kuanwoo/SYMPL64_FloatingPoint_RISC-/FloPoCo_operators/Exp_Clk9.vhdl

-- vagrant@vagrant-ubuntu-trusty-32:~/flopoco-3.0.beta5$ ./flopoco -name=Exp_Clk -frequency=200 -useHardMult=no FPExp 9 23
-- Warning: the given expression is not a constant but an expression to evaluate. A faithful evaluation to 10000 bits will be used.
-- Warning: the given expression is not a constant but an expression to evaluate. A faithful evaluation to 10000 bits will be used.
-- Updating entity name to: Exp_Clk
-- 
-- Final report:
-- Entity SmallMultTableP3x3r6XuYu
--    Not pipelined
-- Entity Compressor_6_3_c
--    Not pipelined
-- Entity Compressor_14_3_d
--    Not pipelined
-- Entity Compressor_4_3_e
--    Not pipelined
-- Entity Compressor_23_3_f
--    Not pipelined
-- Entity Compressor_3_2_a
--    Not pipelined
-- |---Entity LeftShifter_24_by_max_34_uid3
-- |      Not pipelined
-- |   |---Entity FixRealKCM_M3_7_0_1_log_2_unsigned_Table_1
-- |   |      Not pipelined
-- |   |---Entity FixRealKCM_M3_7_0_1_log_2_unsigned_Table_0
-- |   |      Not pipelined
-- |   |---Entity IntAdder_13_f200_uid11
-- |   |      Not pipelined
-- |---Entity FixRealKCM_M3_7_0_1_log_2_unsigned
-- |      Pipeline depth = 1
-- |   |---Entity FixRealKCM_0_8_M26_log_2_unsigned_Table_1
-- |   |      Not pipelined
-- |   |---Entity FixRealKCM_0_8_M26_log_2_unsigned_Table_0
-- |   |      Not pipelined
-- |   |---Entity IntAdder_35_f200_uid24
-- |   |      Pipeline depth = 1
-- |---Entity FixRealKCM_0_8_M26_log_2_unsigned
-- |      Pipeline depth = 1
-- |---Entity IntAdder_26_f219_uid32
-- |      Not pipelined
-- |---Entity MagicSPExpTable
-- |      Not pipelined
-- |---Entity IntAdder_18_f200_uid41
-- |      Not pipelined
-- |---Entity IntAdder_18_f200_uid48
-- |      Not pipelined
-- |   |---Entity IntAdder_24_f200_uid155
-- |   |      Not pipelined
-- |---Entity IntMultiplier_UsingDSP_17_18_19_unsigned_uid55
-- |      Pipeline depth = 1
-- |---Entity IntAdder_27_f200_uid163
-- |      Not pipelined
-- |---Entity IntAdder_34_f200_uid170
-- |      Not pipelined
-- Entity Exp_Clk
--    Pipeline depth = 6
-- Output file: flopoco.vhdl
--------------------------------------------------------------------------------
--                          SmallMultTableP3x3r6XuYu
-- This operator is part of the Infinite Virtual Library FloPoCoLib
-- All rights reserved
-- Authors: Florent de Dinechin (2007-2012)
--------------------------------------------------------------------------------
library ieee;
use ieee.std_logic_1164.all;
use ieee.numeric_std.all;
library work;
entity SmallMultTableP3x3r6XuYu is
   port ( clk, rst : in std_logic;
          X : in  std_logic_vector(5 downto 0);
          Y : out  std_logic_vector(5 downto 0)   );
end entity;

architecture arch of SmallMultTableP3x3r6XuYu is
begin
  with X select  Y <=
   "000000" when "000000",
   "000000" when "000001",
   "000000" when "000010",
   "000000" when "000011",
   "000000" when "000100",
   "000000" when "000101",
   "000000" when "000110",
   "000000" when "000111",
   "000000" when "001000",
   "000001" when "001001",
   "000010" when "001010",
   "000011" when "001011",
   "000100" when "001100",
   "000101" when "001101",
   "000110" when "001110",
   "000111" when "001111",
   "000000" when "010000",
   "000010" when "010001",
   "000100" when "010010",
   "000110" when "010011",
   "001000" when "010100",
   "001010" when "010101",
   "001100" when "010110",
   "001110" when "010111",
   "000000" when "011000",
   "000011" when "011001",
   "000110" when "011010",
   "001001" when "011011",
   "001100" when "011100",
   "001111" when "011101",
   "010010" when "011110",
   "010101" when "011111",
   "000000" when "100000",
   "000100" when "100001",
   "001000" when "100010",
   "001100" when "100011",
   "010000" when "100100",
   "010100" when "100101",
   "011000" when "100110",
   "011100" when "100111",
   "000000" when "101000",
   "000101" when "101001",
   "001010" when "101010",
   "001111" when "101011",
   "010100" when "101100",
   "011001" when "101101",
   "011110" when "101110",
   "100011" when "101111",
   "000000" when "110000",
   "000110" when "110001",
   "001100" when "110010",
   "010010" when "110011",
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
use ieee.std_logic_unsigned.all;
library std;
use std.textio.all;
library work;

entity Compressor_14_3_d is
   port ( X0 : in  std_logic_vector(3 downto 0);
          X1 : in  std_logic_vector(0 downto 0);
          R : out  std_logic_vector(2 downto 0)   );
end entity;

architecture arch of Compressor_14_3_d is
signal X :  std_logic_vector(4 downto 0);
begin
   X <=X1 & X0 ;
   with X select R <=
      "000" when "00000",
      "001" when "00001",
      "001" when "00010",
      "010" when "00011",
      "001" when "00100",
      "010" when "00101",
      "010" when "00110",
      "011" when "00111",
      "001" when "01000",
      "010" when "01001",
      "010" when "01010",
      "011" when "01011",
      "010" when "01100",
      "011" when "01101",
      "011" when "01110",
      "100" when "01111",
      "010" when "10000",
      "011" when "10001",
      "011" when "10010",
      "100" when "10011",
      "011" when "10100",
      "100" when "10101",
      "100" when "10110",
      "101" when "10111",
      "011" when "11000",
      "100" when "11001",
      "100" when "11010",
      "101" when "11011",
      "100" when "11100",
      "101" when "11101",
      "101" when "11110",
      "110" when "11111",
      "---" when others;

end architecture;

--------------------------------------------------------------------------------
--                               Compressor_4_3_e
-- This operator is part of the Infinite Virtual Library FloPoCoLib
-- All rights reserved
-- Authors: Bogdan Popa, Illyes Kinga, 2012
--------------------------------------------------------------------------------
-- combinatorial

library ieee;
use ieee.std_logic_1164.all;
use ieee.std_logic_arith.all;
use ieee.std_logic_unsigned.all;
library std;
use std.textio.all;
library work;

entity Compressor_4_3_e is
   port ( X0 : in  std_logic_vector(3 downto 0);
          R : out  std_logic_vector(2 downto 0)   );
end entity;

architecture arch of Compressor_4_3_e is
signal X :  std_logic_vector(3 downto 0);
begin
   X <=X0 ;
   with X select R <=
      "000" when "0000",
      "001" when "0001",
      "001" when "0010",
      "010" when "0011",
      "001" when "0100",
      "010" when "0101",
      "010" when "0110",
      "011" when "0111",
      "001" when "1000",
      "010" when "1001",
      "010" when "1010",
      "011" when "1011",
      "010" when "1100",
      "011" when "1101",
      "011" when "1110",
      "100" when "1111",
      "---" when others;

end architecture;

--------------------------------------------------------------------------------
--                              Compressor_23_3_f
-- This operator is part of the Infinite Virtual Library FloPoCoLib
-- All rights reserved
-- Authors: Bogdan Popa, Illyes Kinga, 2012
--------------------------------------------------------------------------------
-- combinatorial

library ieee;
use ieee.std_logic_1164.all;
use ieee.std_logic_arith.all;
use ieee.std_logic_unsigned.all;
library std;
use std.textio.all;
library work;

entity Compressor_23_3_f is
   port ( X0 : in  std_logic_vector(2 downto 0);
          X1 : in  std_logic_vector(1 downto 0);
          R : out  std_logic_vector(2 downto 0)   );
end entity;

architecture arch of Compressor_23_3_f is
signal X :  std_logic_vector(4 downto 0);
begin
   X <=X1 & X0 ;
   with X select R <=
      "000" when "00000",
      "001" when "00001",
      "001" when "00010",
      "010" when "00011",
      "001" when "00100",
      "010" when "00101",
      "010" when "00110",
      "011" when "00111",
      "010" when "01000",
      "011" when "01001",
      "011" when "01010",
      "100" when "01011",
      "011" when "01100",
      "100" when "01101",
      "100" when "01110",
      "101" when "01111",
      "010" when "10000",
      "011" when "10001",
      "011" when "10010",
      "100" when "10011",
      "011" when "10100",
      "100" when "10101",
      "100" when "10110",
      "101" when "10111",
      "100" when "11000",
      "101" when "11001",
      "101" when "11010",
      "110" when "11011",
      "101" when "11100",
      "110" when "11101",
      "110" when "11110",
      "111" when "11111",
      "---" when others;

end architecture;

--------------------------------------------------------------------------------
--                               Compressor_3_2_a
-- This operator is part of the Infinite Virtual Library FloPoCoLib
-- All rights reserved
-- Authors: Bogdan Popa, Illyes Kinga, 2012
--------------------------------------------------------------------------------
-- combinatorial

library ieee;
use ieee.std_logic_1164.all;
use ieee.std_logic_arith.all;
use ieee.std_logic_unsigned.all;
library std;
use std.textio.all;
library work;

entity Compressor_3_2_a is
   port ( X0 : in  std_logic_vector(2 downto 0);
          R : out  std_logic_vector(1 downto 0)   );
end entity;

architecture arch of Compressor_3_2_a is
signal X :  std_logic_vector(2 downto 0);
begin
   X <=X0 ;
   with X select R <=
      "00" when "000",
      "01" when "001",
      "01" when "010",
      "10" when "011",
      "01" when "100",
      "10" when "101",
      "10" when "110",
      "11" when "111",
      "--" when others;

end architecture;

--------------------------------------------------------------------------------
--                       LeftShifter_24_by_max_34_uid3
-- This operator is part of the Infinite Virtual Library FloPoCoLib
-- All rights reserved
-- Authors: Bogdan Pasca, Florent de Dinechin (2008-2011)
--------------------------------------------------------------------------------
-- Pipeline depth: 0 cycles

library ieee;
use ieee.std_logic_1164.all;
use ieee.std_logic_arith.all;
use ieee.std_logic_unsigned.all;
library std;
use std.textio.all;
library work;

entity LeftShifter_24_by_max_34_uid3 is
   port ( clk, rst : in std_logic;
          X : in  std_logic_vector(23 downto 0);
          S : in  std_logic_vector(5 downto 0);
          R : out  std_logic_vector(57 downto 0)   );
end entity;

architecture arch of LeftShifter_24_by_max_34_uid3 is
signal level0 :  std_logic_vector(23 downto 0);
signal ps :  std_logic_vector(5 downto 0);
signal level1 :  std_logic_vector(24 downto 0);
signal level2 :  std_logic_vector(26 downto 0);
signal level3 :  std_logic_vector(30 downto 0);
signal level4 :  std_logic_vector(38 downto 0);
signal level5 :  std_logic_vector(54 downto 0);
signal level6 :  std_logic_vector(86 downto 0);
begin
   process(clk)
      begin
         if clk'event and clk = '1' then
         end if;
      end process;
   level0<= X;
   ps<= S;
   level1<= level0 & (0 downto 0 => '0') when ps(0)= '1' else     (0 downto 0 => '0') & level0;
   level2<= level1 & (1 downto 0 => '0') when ps(1)= '1' else     (1 downto 0 => '0') & level1;
   level3<= level2 & (3 downto 0 => '0') when ps(2)= '1' else     (3 downto 0 => '0') & level2;
   level4<= level3 & (7 downto 0 => '0') when ps(3)= '1' else     (7 downto 0 => '0') & level3;
   level5<= level4 & (15 downto 0 => '0') when ps(4)= '1' else     (15 downto 0 => '0') & level4;
   level6<= level5 & (31 downto 0 => '0') when ps(5)= '1' else     (31 downto 0 => '0') & level5;
   R <= level6(57 downto 0);
end architecture;

--------------------------------------------------------------------------------
--                 FixRealKCM_M3_7_0_1_log_2_unsigned_Table_1
-- This operator is part of the Infinite Virtual Library FloPoCoLib
-- All rights reserved
-- Authors: Florent de Dinechin (2007-2012)
--------------------------------------------------------------------------------
library ieee;
use ieee.std_logic_1164.all;
use ieee.numeric_std.all;
library work;
entity FixRealKCM_M3_7_0_1_log_2_unsigned_Table_1 is
   port ( clk, rst : in std_logic;
          X : in  std_logic_vector(4 downto 0);
          Y : out  std_logic_vector(12 downto 0)   );
end entity;

architecture arch of FixRealKCM_M3_7_0_1_log_2_unsigned_Table_1 is
begin
  with X select  Y <=
   "0000000001000" when "00000",
   "0000011000001" when "00001",
   "0000101111001" when "00010",
   "0001000110010" when "00011",
   "0001011101011" when "00100",
   "0001110100011" when "00101",
   "0010001011100" when "00110",
   "0010100010101" when "00111",
   "0010111001101" when "01000",
   "0011010000110" when "01001",
   "0011100111111" when "01010",
   "0011111110111" when "01011",
   "0100010110000" when "01100",
   "0100101101001" when "01101",
   "0101000100001" when "01110",
   "0101011011010" when "01111",
   "0101110010011" when "10000",
   "0110001001011" when "10001",
   "0110100000100" when "10010",
   "0110110111101" when "10011",
   "0111001110101" when "10100",
   "0111100101110" when "10101",
   "0111111100111" when "10110",
   "1000010011111" when "10111",
   "1000101011000" when "11000",
   "1001000010001" when "11001",
   "1001011001001" when "11010",
   "1001110000010" when "11011",
   "1010000111011" when "11100",
   "1010011110011" when "11101",
   "1010110101100" when "11110",
   "1011001100101" when "11111",
   "-------------" when others;
end architecture;

--------------------------------------------------------------------------------
--                 FixRealKCM_M3_7_0_1_log_2_unsigned_Table_0
-- This operator is part of the Infinite Virtual Library FloPoCoLib
-- All rights reserved
-- Authors: Florent de Dinechin (2007-2012)
--------------------------------------------------------------------------------
library ieee;
use ieee.std_logic_1164.all;
use ieee.numeric_std.all;
library work;
entity FixRealKCM_M3_7_0_1_log_2_unsigned_Table_0 is
   port ( clk, rst : in std_logic;
          X : in  std_logic_vector(5 downto 0);
          Y : out  std_logic_vector(7 downto 0)   );
end entity;

architecture arch of FixRealKCM_M3_7_0_1_log_2_unsigned_Table_0 is
begin
  with X select  Y <=
   "00000000" when "000000",
   "00000011" when "000001",
   "00000110" when "000010",
   "00001001" when "000011",
   "00001100" when "000100",
   "00001110" when "000101",
   "00010001" when "000110",
   "00010100" when "000111",
   "00010111" when "001000",
   "00011010" when "001001",
   "00011101" when "001010",
   "00100000" when "001011",
   "00100011" when "001100",
   "00100110" when "001101",
   "00101000" when "001110",
   "00101011" when "001111",
   "00101110" when "010000",
   "00110001" when "010001",
   "00110100" when "010010",
   "00110111" when "010011",
   "00111010" when "010100",
   "00111101" when "010101",
   "00111111" when "010110",
   "01000010" when "010111",
   "01000101" when "011000",
   "01001000" when "011001",
   "01001011" when "011010",
   "01001110" when "011011",
   "01010001" when "011100",
   "01010100" when "011101",
   "01010111" when "011110",
   "01011001" when "011111",
   "01011100" when "100000",
   "01011111" when "100001",
   "01100010" when "100010",
   "01100101" when "100011",
   "01101000" when "100100",
   "01101011" when "100101",
   "01101110" when "100110",
   "01110001" when "100111",
   "01110011" when "101000",
   "01110110" when "101001",
   "01111001" when "101010",
   "01111100" when "101011",
   "01111111" when "101100",
   "10000010" when "101101",
   "10000101" when "101110",
   "10001000" when "101111",
   "10001010" when "110000",
   "10001101" when "110001",
   "10010000" when "110010",
   "10010011" when "110011",
   "10010110" when "110100",
   "10011001" when "110101",
   "10011100" when "110110",
   "10011111" when "110111",
   "10100010" when "111000",
   "10100100" when "111001",
   "10100111" when "111010",
   "10101010" when "111011",
   "10101101" when "111100",
   "10110000" when "111101",
   "10110011" when "111110",
   "10110110" when "111111",
   "--------" when others;
end architecture;

--------------------------------------------------------------------------------
--                           IntAdder_13_f200_uid11
--                    (IntAdderAlternative_13_f200_uid15)
-- This operator is part of the Infinite Virtual Library FloPoCoLib
-- All rights reserved
-- Authors: Bogdan Pasca, Florent de Dinechin (2008-2010)
--------------------------------------------------------------------------------
-- Pipeline depth: 0 cycles

library ieee;
use ieee.std_logic_1164.all;
use ieee.std_logic_arith.all;
use ieee.std_logic_unsigned.all;
library std;
use std.textio.all;
library work;

entity IntAdder_13_f200_uid11 is
   port ( clk, rst : in std_logic;
          X : in  std_logic_vector(12 downto 0);
          Y : in  std_logic_vector(12 downto 0);
          Cin : in  std_logic;
          R : out  std_logic_vector(12 downto 0)   );
end entity;

architecture arch of IntAdder_13_f200_uid11 is
begin
   process(clk)
      begin
         if clk'event and clk = '1' then
         end if;
      end process;
   --Alternative
    R <= X + Y + Cin;
end architecture;

--------------------------------------------------------------------------------
--                     FixRealKCM_M3_7_0_1_log_2_unsigned
-- This operator is part of the Infinite Virtual Library FloPoCoLib
-- All rights reserved
-- Authors:
--------------------------------------------------------------------------------
-- Pipeline depth: 1 cycles

library ieee;
use ieee.std_logic_1164.all;
use ieee.std_logic_arith.all;
use ieee.std_logic_unsigned.all;
library std;
use std.textio.all;
library work;

entity FixRealKCM_M3_7_0_1_log_2_unsigned is
   port ( clk, rst : in std_logic;
          X : in  std_logic_vector(10 downto 0);
          R : out  std_logic_vector(8 downto 0)   );
end entity;

architecture arch of FixRealKCM_M3_7_0_1_log_2_unsigned is
   component FixRealKCM_M3_7_0_1_log_2_unsigned_Table_0 is
      port ( clk, rst : in std_logic;
             X : in  std_logic_vector(5 downto 0);
             Y : out  std_logic_vector(7 downto 0)   );
   end component;

   component FixRealKCM_M3_7_0_1_log_2_unsigned_Table_1 is
      port ( clk, rst : in std_logic;
             X : in  std_logic_vector(4 downto 0);
             Y : out  std_logic_vector(12 downto 0)   );
   end component;

   component IntAdder_13_f200_uid11 is
      port ( clk, rst : in std_logic;
             X : in  std_logic_vector(12 downto 0);
             Y : in  std_logic_vector(12 downto 0);
             Cin : in  std_logic;
             R : out  std_logic_vector(12 downto 0)   );
   end component;

signal d1 :  std_logic_vector(4 downto 0);
signal d0 :  std_logic_vector(5 downto 0);
signal pp0, pp0_d1 :  std_logic_vector(7 downto 0);
signal pp1, pp1_d1 :  std_logic_vector(12 downto 0);
signal addOp0 :  std_logic_vector(12 downto 0);
signal OutRes :  std_logic_vector(12 downto 0);
attribute rom_extract: string;
attribute rom_style: string;
attribute rom_extract of FixRealKCM_M3_7_0_1_log_2_unsigned_Table_0: component is "yes";
attribute rom_extract of FixRealKCM_M3_7_0_1_log_2_unsigned_Table_1: component is "yes";
attribute rom_style of FixRealKCM_M3_7_0_1_log_2_unsigned_Table_0: component is "distributed";
attribute rom_style of FixRealKCM_M3_7_0_1_log_2_unsigned_Table_1: component is "distributed";
begin
   process(clk)
      begin
         if clk'event and clk = '1' then
            pp0_d1 <=  pp0;
            pp1_d1 <=  pp1;
         end if;
      end process;
   d1 <= X(10 downto 6);
   d0 <= X(5 downto 0);
   KCMTable_0: FixRealKCM_M3_7_0_1_log_2_unsigned_Table_0  -- pipelineDepth=0 maxInDelay=0
      port map ( clk  => clk,
                 rst  => rst,
                 X => d0,
                 Y => pp0);
   KCMTable_1: FixRealKCM_M3_7_0_1_log_2_unsigned_Table_1  -- pipelineDepth=0 maxInDelay=0
      port map ( clk  => clk,
                 rst  => rst,
                 X => d1,
                 Y => pp1);
   ----------------Synchro barrier, entering cycle 1----------------
   addOp0 <= (12 downto 8 => '0') & pp0_d1;
   Result_Adder: IntAdder_13_f200_uid11  -- pipelineDepth=0 maxInDelay=1.08008e-09
      port map ( clk  => clk,
                 rst  => rst,
                 Cin => '0',
                 R => OutRes,
                 X => addOp0,
                 Y => pp1_d1);
   R <= OutRes(12 downto 4);
end architecture;

--------------------------------------------------------------------------------
--                 FixRealKCM_0_8_M26_log_2_unsigned_Table_1
-- This operator is part of the Infinite Virtual Library FloPoCoLib
-- All rights reserved
-- Authors: Florent de Dinechin (2007-2012)
--------------------------------------------------------------------------------
library ieee;
use ieee.std_logic_1164.all;
use ieee.numeric_std.all;
library work;
entity FixRealKCM_0_8_M26_log_2_unsigned_Table_1 is
   port ( clk, rst : in std_logic;
          X : in  std_logic_vector(2 downto 0);
          Y : out  std_logic_vector(34 downto 0)   );
end entity;

architecture arch of FixRealKCM_0_8_M26_log_2_unsigned_Table_1 is
begin
  with X select  Y <=
   "00000000000000000000000000000000000" when "000",
   "00010110001011100100001011111111000" when "001",
   "00101100010111001000010111111110000" when "010",
   "01000010100010101100100011111100111" when "011",
   "01011000101110010000101111111011111" when "100",
   "01101110111001110100111011111010111" when "101",
   "10000101000101011001000111111001111" when "110",
   "10011011010000111101010011111000111" when "111",
   "-----------------------------------" when others;
end architecture;

--------------------------------------------------------------------------------
--                 FixRealKCM_0_8_M26_log_2_unsigned_Table_0
-- This operator is part of the Infinite Virtual Library FloPoCoLib
-- All rights reserved
-- Authors: Florent de Dinechin (2007-2012)
--------------------------------------------------------------------------------
library ieee;
use ieee.std_logic_1164.all;
use ieee.numeric_std.all;
library work;
entity FixRealKCM_0_8_M26_log_2_unsigned_Table_0 is
   port ( clk, rst : in std_logic;
          X : in  std_logic_vector(5 downto 0);
          Y : out  std_logic_vector(31 downto 0)   );
end entity;

architecture arch of FixRealKCM_0_8_M26_log_2_unsigned_Table_0 is
begin
  with X select  Y <=
   "00000000000000000000000000000000" when "000000",
   "00000010110001011100100001100000" when "000001",
   "00000101100010111001000011000000" when "000010",
   "00001000010100010101100100100000" when "000011",
   "00001011000101110010000101111111" when "000100",
   "00001101110111001110100111011111" when "000101",
   "00010000101000101011001000111111" when "000110",
   "00010011011010000111101010011111" when "000111",
   "00010110001011100100001011111111" when "001000",
   "00011000111101000000101101011111" when "001001",
   "00011011101110011101001110111111" when "001010",
   "00011110011111111001110000011111" when "001011",
   "00100001010001010110010001111110" when "001100",
   "00100100000010110010110011011110" when "001101",
   "00100110110100001111010100111110" when "001110",
   "00101001100101101011110110011110" when "001111",
   "00101100010111001000010111111110" when "010000",
   "00101111001000100100111001011110" when "010001",
   "00110001111010000001011010111110" when "010010",
   "00110100101011011101111100011110" when "010011",
   "00110111011100111010011101111101" when "010100",
   "00111010001110010110111111011101" when "010101",
   "00111100111111110011100000111101" when "010110",
   "00111111110001010000000010011101" when "010111",
   "01000010100010101100100011111101" when "011000",
   "01000101010100001001000101011101" when "011001",
   "01001000000101100101100110111101" when "011010",
   "01001010110111000010001000011101" when "011011",
   "01001101101000011110101001111100" when "011100",
   "01010000011001111011001011011100" when "011101",
   "01010011001011010111101100111100" when "011110",
   "01010101111100110100001110011100" when "011111",
   "01011000101110010000101111111100" when "100000",
   "01011011011111101101010001011100" when "100001",
   "01011110010001001001110010111100" when "100010",
   "01100001000010100110010100011100" when "100011",
   "01100011110100000010110101111011" when "100100",
   "01100110100101011111010111011011" when "100101",
   "01101001010110111011111000111011" when "100110",
   "01101100001000011000011010011011" when "100111",
   "01101110111001110100111011111011" when "101000",
   "01110001101011010001011101011011" when "101001",
   "01110100011100101101111110111011" when "101010",
   "01110111001110001010100000011011" when "101011",
   "01111001111111100111000001111010" when "101100",
   "01111100110001000011100011011010" when "101101",
   "01111111100010100000000100111010" when "101110",
   "10000010010011111100100110011010" when "101111",
   "10000101000101011001000111111010" when "110000",
   "10000111110110110101101001011010" when "110001",
   "10001010101000010010001010111010" when "110010",
   "10001101011001101110101100011001" when "110011",
   "10010000001011001011001101111001" when "110100",
   "10010010111100100111101111011001" when "110101",
   "10010101101110000100010000111001" when "110110",
   "10011000011111100000110010011001" when "110111",
   "10011011010000111101010011111001" when "111000",
   "10011110000010011001110101011001" when "111001",
   "10100000110011110110010110111001" when "111010",
   "10100011100101010010111000011000" when "111011",
   "10100110010110101111011001111000" when "111100",
   "10101001001000001011111011011000" when "111101",
   "10101011111001101000011100111000" when "111110",
   "10101110101011000100111110011000" when "111111",
   "--------------------------------" when others;
end architecture;

--------------------------------------------------------------------------------
--                           IntAdder_35_f200_uid24
--                     (IntAdderClassical_35_f200_uid26)
-- This operator is part of the Infinite Virtual Library FloPoCoLib
-- All rights reserved
-- Authors: Bogdan Pasca, Florent de Dinechin (2008-2010)
--------------------------------------------------------------------------------
-- Pipeline depth: 1 cycles

library ieee;
use ieee.std_logic_1164.all;
use ieee.std_logic_arith.all;
use ieee.std_logic_unsigned.all;
library std;
use std.textio.all;
library work;

entity IntAdder_35_f200_uid24 is
   port ( clk, rst : in std_logic;
          X : in  std_logic_vector(34 downto 0);
          Y : in  std_logic_vector(34 downto 0);
          Cin : in  std_logic;
          R : out  std_logic_vector(34 downto 0)   );
end entity;

architecture arch of IntAdder_35_f200_uid24 is
signal X_d1 :  std_logic_vector(34 downto 0);
signal Y_d1 :  std_logic_vector(34 downto 0);
signal Cin_d1 :  std_logic;
begin
   process(clk)
      begin
         if clk'event and clk = '1' then
            X_d1 <=  X;
            Y_d1 <=  Y;
            Cin_d1 <=  Cin;
         end if;
      end process;
   --Classical
   ----------------Synchro barrier, entering cycle 1----------------
    R <= X_d1 + Y_d1 + Cin_d1;
end architecture;

--------------------------------------------------------------------------------
--                     FixRealKCM_0_8_M26_log_2_unsigned
-- This operator is part of the Infinite Virtual Library FloPoCoLib
-- All rights reserved
-- Authors:
--------------------------------------------------------------------------------
-- Pipeline depth: 1 cycles

library ieee;
use ieee.std_logic_1164.all;
use ieee.std_logic_arith.all;
use ieee.std_logic_unsigned.all;
library std;
use std.textio.all;
library work;

entity FixRealKCM_0_8_M26_log_2_unsigned is
   port ( clk, rst : in std_logic;
          X : in  std_logic_vector(8 downto 0);
          R : out  std_logic_vector(34 downto 0)   );
end entity;

architecture arch of FixRealKCM_0_8_M26_log_2_unsigned is
   component FixRealKCM_0_8_M26_log_2_unsigned_Table_0 is
      port ( clk, rst : in std_logic;
             X : in  std_logic_vector(5 downto 0);
             Y : out  std_logic_vector(31 downto 0)   );
   end component;

   component FixRealKCM_0_8_M26_log_2_unsigned_Table_1 is
      port ( clk, rst : in std_logic;
             X : in  std_logic_vector(2 downto 0);
             Y : out  std_logic_vector(34 downto 0)   );
   end component;

   component IntAdder_35_f200_uid24 is
      port ( clk, rst : in std_logic;
             X : in  std_logic_vector(34 downto 0);
             Y : in  std_logic_vector(34 downto 0);
             Cin : in  std_logic;
             R : out  std_logic_vector(34 downto 0)   );
   end component;

signal d1 :  std_logic_vector(2 downto 0);
signal d0 :  std_logic_vector(5 downto 0);
signal pp0 :  std_logic_vector(31 downto 0);
signal pp1 :  std_logic_vector(34 downto 0);
signal addOp0 :  std_logic_vector(34 downto 0);
signal OutRes :  std_logic_vector(34 downto 0);
attribute rom_extract: string;
attribute rom_style: string;
attribute rom_extract of FixRealKCM_0_8_M26_log_2_unsigned_Table_0: component is "yes";
attribute rom_extract of FixRealKCM_0_8_M26_log_2_unsigned_Table_1: component is "yes";
attribute rom_style of FixRealKCM_0_8_M26_log_2_unsigned_Table_0: component is "distributed";
attribute rom_style of FixRealKCM_0_8_M26_log_2_unsigned_Table_1: component is "distributed";
begin
   process(clk)
      begin
         if clk'event and clk = '1' then
         end if;
      end process;
   d1 <= X(8 downto 6);
   d0 <= X(5 downto 0);
   KCMTable_0: FixRealKCM_0_8_M26_log_2_unsigned_Table_0  -- pipelineDepth=0 maxInDelay=0
      port map ( clk  => clk,
                 rst  => rst,
                 X => d0,
                 Y => pp0);
   KCMTable_1: FixRealKCM_0_8_M26_log_2_unsigned_Table_1  -- pipelineDepth=0 maxInDelay=0
      port map ( clk  => clk,
                 rst  => rst,
                 X => d1,
                 Y => pp1);
   addOp0 <= (34 downto 32 => '0') & pp0;
   Result_Adder: IntAdder_35_f200_uid24  -- pipelineDepth=1 maxInDelay=3.93836e-09
      port map ( clk  => clk,
                 rst  => rst,
                 Cin => '0',
                 R => OutRes,
                 X => addOp0,
                 Y => pp1);
   ----------------Synchro barrier, entering cycle 1----------------
   R <= OutRes(34 downto 0);
end architecture;

--------------------------------------------------------------------------------
--                           IntAdder_26_f219_uid32
--                    (IntAdderAlternative_26_f219_uid36)
-- This operator is part of the Infinite Virtual Library FloPoCoLib
-- All rights reserved
-- Authors: Bogdan Pasca, Florent de Dinechin (2008-2010)
--------------------------------------------------------------------------------
-- Pipeline depth: 0 cycles

library ieee;
use ieee.std_logic_1164.all;
use ieee.std_logic_arith.all;
use ieee.std_logic_unsigned.all;
library std;
use std.textio.all;
library work;

entity IntAdder_26_f219_uid32 is
   port ( clk, rst : in std_logic;
          X : in  std_logic_vector(25 downto 0);
          Y : in  std_logic_vector(25 downto 0);
          Cin : in  std_logic;
          R : out  std_logic_vector(25 downto 0)   );
end entity;

architecture arch of IntAdder_26_f219_uid32 is
begin
   process(clk)
      begin
         if clk'event and clk = '1' then
         end if;
      end process;
   --Alternative
    R <= X + Y + Cin;
end architecture;

--------------------------------------------------------------------------------
--                              MagicSPExpTable
-- This operator is part of the Infinite Virtual Library FloPoCoLib
-- All rights reserved
-- Authors: Radu Tudoran, Florent de Dinechin (2009)
--------------------------------------------------------------------------------
-- combinatorial

library ieee;
use ieee.std_logic_1164.all;
use ieee.std_logic_arith.all;
use ieee.std_logic_unsigned.all;
library std;
use std.textio.all;
library work;

entity MagicSPExpTable is
   port ( X1 : in  std_logic_vector(8 downto 0);
          Y1 : out  std_logic_vector(35 downto 0);
          X2 : in  std_logic_vector(8 downto 0);
          Y2 : out  std_logic_vector(35 downto 0)   );
end entity;

architecture arch of MagicSPExpTable is
type ROMContent is array (0 to 511) of std_logic_vector(35 downto 0);
constant memVar: ROMContent :=    (
      "100000000000000000000000000000000000",       "100000000100000000010000000000000000",       "100000001000000001000000001000000000",       "100000001100000010010000010000000000",
      "100000010000000100000000101000000000",       "100000010100000110010001010000000000",       "100000011000001001000010010000000000",       "100000011100001100010011101000000000",
      "100000100000010000000101011000000000",       "100000100100010100010111101000000000",       "100000101000011001001010100000000000",       "100000101100011110011110000000000000",
      "100000110000100100010010001000000000",       "100000110100101010100111000000000000",       "100000111000110001011100110000000000",       "100000111100111000110011011000000000",
      "100001000001000000101011000000000000",       "100001000101001001000011101000000000",       "100001001001010001111101010000000000",       "100001001101011011011000001000000000",
      "100001010001100101010100001000000000",       "100001010101101111110001100000000000",       "100001011001111010110000001000000000",       "100001011110000110010000001000000000",
      "100001100010010010010001110000000000",       "100001100110011110110100110000000000",       "100001101010101011111001011000000000",       "100001101110111001011111110000000000",
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
          R : out  std_logic_vector(17 downto 0)   );
end entity;

architecture arch of IntAdder_18_f200_uid41 is
begin
   process(clk)
      begin
         if clk'event and clk = '1' then
         end if;
      end process;
   --Alternative
    R <= X + Y + Cin;
end architecture;

--------------------------------------------------------------------------------
--                           IntAdder_18_f200_uid48
--                    (IntAdderAlternative_18_f200_uid52)
-- This operator is part of the Infinite Virtual Library FloPoCoLib
-- All rights reserved
-- Authors: Bogdan Pasca, Florent de Dinechin (2008-2010)
--------------------------------------------------------------------------------
-- Pipeline depth: 0 cycles

library ieee;
use ieee.std_logic_1164.all;
use ieee.std_logic_arith.all;
use ieee.std_logic_unsigned.all;
library std;
use std.textio.all;
library work;

entity IntAdder_18_f200_uid48 is
   port ( clk, rst : in std_logic;
          X : in  std_logic_vector(17 downto 0);
          Y : in  std_logic_vector(17 downto 0);
          Cin : in  std_logic;
          R : out  std_logic_vector(17 downto 0)   );
end entity;

architecture arch of IntAdder_18_f200_uid48 is
begin
   process(clk)
      begin
         if clk'event and clk = '1' then
         end if;
      end process;
   --Alternative
    R <= X + Y + Cin;
end architecture;

--------------------------------------------------------------------------------
--                          IntAdder_24_f200_uid155
--                    (IntAdderAlternative_24_f200_uid159)
-- This operator is part of the Infinite Virtual Library FloPoCoLib
-- All rights reserved
-- Authors: Bogdan Pasca, Florent de Dinechin (2008-2010)
--------------------------------------------------------------------------------
-- Pipeline depth: 0 cycles

library ieee;
use ieee.std_logic_1164.all;
use ieee.std_logic_arith.all;
use ieee.std_logic_unsigned.all;
library std;
use std.textio.all;
library work;

entity IntAdder_24_f200_uid155 is
   port ( clk, rst : in std_logic;
          X : in  std_logic_vector(23 downto 0);
          Y : in  std_logic_vector(23 downto 0);
          Cin : in  std_logic;
          R : out  std_logic_vector(23 downto 0)   );
end entity;

architecture arch of IntAdder_24_f200_uid155 is
begin
   process(clk)
      begin
         if clk'event and clk = '1' then
         end if;
      end process;
   --Alternative
    R <= X + Y + Cin;
end architecture;

--------------------------------------------------------------------------------
--               IntMultiplier_UsingDSP_17_18_19_unsigned_uid55
-- This operator is part of the Infinite Virtual Library FloPoCoLib
-- All rights reserved
-- Authors: Florent de Dinechin, Kinga Illyes, Bogdan Popa, Bogdan Pasca, 2012
--------------------------------------------------------------------------------
-- Pipeline depth: 1 cycles

library ieee;
use ieee.std_logic_1164.all;
use ieee.numeric_std.all;
library std;
use std.textio.all;
library work;

entity IntMultiplier_UsingDSP_17_18_19_unsigned_uid55 is
   port ( clk, rst : in std_logic;
          X : in  std_logic_vector(16 downto 0);
          Y : in  std_logic_vector(17 downto 0);
          R : out  std_logic_vector(18 downto 0)   );
end entity;

architecture arch of IntMultiplier_UsingDSP_17_18_19_unsigned_uid55 is
   component Compressor_14_3_d is
      port ( X0 : in  std_logic_vector(3 downto 0);
             X1 : in  std_logic_vector(0 downto 0);
             R : out  std_logic_vector(2 downto 0)   );
   end component;

   component Compressor_23_3_f is
      port ( X0 : in  std_logic_vector(2 downto 0);
             X1 : in  std_logic_vector(1 downto 0);
             R : out  std_logic_vector(2 downto 0)   );
   end component;

   component Compressor_3_2_a is
      port ( X0 : in  std_logic_vector(2 downto 0);
             R : out  std_logic_vector(1 downto 0)   );
   end component;

   component Compressor_4_3_e is
      port ( X0 : in  std_logic_vector(3 downto 0);
             R : out  std_logic_vector(2 downto 0)   );
   end component;

   component Compressor_6_3_c is
      port ( X0 : in  std_logic_vector(5 downto 0);
             R : out  std_logic_vector(2 downto 0)   );
   end component;

   component IntAdder_24_f200_uid155 is
      port ( clk, rst : in std_logic;
             X : in  std_logic_vector(23 downto 0);
             Y : in  std_logic_vector(23 downto 0);
             Cin : in  std_logic;
             R : out  std_logic_vector(23 downto 0)   );
   end component;

   component SmallMultTableP3x3r6XuYu is
      port ( clk, rst : in std_logic;
             X : in  std_logic_vector(5 downto 0);
             Y : out  std_logic_vector(5 downto 0)   );
   end component;

signal XX_m56 :  std_logic_vector(17 downto 0);
signal YY_m56 :  std_logic_vector(16 downto 0);
signal Xp_m56b58 :  std_logic_vector(17 downto 0);
signal Yp_m56b58 :  std_logic_vector(17 downto 0);
signal x_m56b58_0 :  std_logic_vector(2 downto 0);
signal x_m56b58_1 :  std_logic_vector(2 downto 0);
signal x_m56b58_2 :  std_logic_vector(2 downto 0);
signal x_m56b58_3 :  std_logic_vector(2 downto 0);
signal x_m56b58_4 :  std_logic_vector(2 downto 0);
signal x_m56b58_5 :  std_logic_vector(2 downto 0);
signal y_m56b58_0 :  std_logic_vector(2 downto 0);
signal y_m56b58_1 :  std_logic_vector(2 downto 0);
signal y_m56b58_2 :  std_logic_vector(2 downto 0);
signal y_m56b58_3 :  std_logic_vector(2 downto 0);
signal y_m56b58_4 :  std_logic_vector(2 downto 0);
signal y_m56b58_5 :  std_logic_vector(2 downto 0);
signal Y0X3_58_m56 :  std_logic_vector(5 downto 0);
signal PP58X3Y0_m56 :  std_logic_vector(5 downto 0);
signal heap_bh57_w0_0 :  std_logic;
signal heap_bh57_w1_0 :  std_logic;
signal heap_bh57_w2_0 :  std_logic;
signal Y0X4_58_m56 :  std_logic_vector(5 downto 0);
signal PP58X4Y0_m56 :  std_logic_vector(5 downto 0);
signal heap_bh57_w1_1 :  std_logic;
signal heap_bh57_w2_1 :  std_logic;
signal heap_bh57_w3_0 :  std_logic;
signal heap_bh57_w4_0 :  std_logic;
signal heap_bh57_w5_0 :  std_logic;
signal Y0X5_58_m56 :  std_logic_vector(5 downto 0);
signal PP58X5Y0_m56 :  std_logic_vector(5 downto 0);
signal heap_bh57_w4_1 :  std_logic;
signal heap_bh57_w5_1 :  std_logic;
signal heap_bh57_w6_0 :  std_logic;
signal heap_bh57_w7_0 :  std_logic;
signal heap_bh57_w8_0 :  std_logic;
signal Y1X2_58_m56 :  std_logic_vector(5 downto 0);
signal PP58X2Y1_m56 :  std_logic_vector(5 downto 0);
signal heap_bh57_w0_1 :  std_logic;
signal heap_bh57_w1_2 :  std_logic;
signal heap_bh57_w2_2 :  std_logic;
signal Y1X3_58_m56 :  std_logic_vector(5 downto 0);
signal PP58X3Y1_m56 :  std_logic_vector(5 downto 0);
signal heap_bh57_w0_2 :  std_logic;
signal heap_bh57_w1_3 :  std_logic;
signal heap_bh57_w2_3 :  std_logic;
signal heap_bh57_w3_1 :  std_logic;
signal heap_bh57_w4_2 :  std_logic;
signal heap_bh57_w5_2 :  std_logic;
signal Y1X4_58_m56 :  std_logic_vector(5 downto 0);
signal PP58X4Y1_m56 :  std_logic_vector(5 downto 0);
signal heap_bh57_w3_2 :  std_logic;
signal heap_bh57_w4_3 :  std_logic;
signal heap_bh57_w5_3 :  std_logic;
signal heap_bh57_w6_1 :  std_logic;
signal heap_bh57_w7_1 :  std_logic;
signal heap_bh57_w8_1 :  std_logic;
signal Y1X5_58_m56 :  std_logic_vector(5 downto 0);
signal PP58X5Y1_m56 :  std_logic_vector(5 downto 0);
signal heap_bh57_w6_2 :  std_logic;
signal heap_bh57_w7_2 :  std_logic;
signal heap_bh57_w8_2 :  std_logic;
signal heap_bh57_w9_0 :  std_logic;
signal heap_bh57_w10_0 :  std_logic;
signal heap_bh57_w11_0 :  std_logic;
signal Y2X1_58_m56 :  std_logic_vector(5 downto 0);
signal PP58X1Y2_m56 :  std_logic_vector(5 downto 0);
signal heap_bh57_w0_3 :  std_logic;
signal heap_bh57_w1_4 :  std_logic;
signal heap_bh57_w2_4 :  std_logic;
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
signal heap_bh57_w22_1, heap_bh57_w22_1_d1 :  std_logic;
signal CompressorIn_bh57_53_82 :  std_logic_vector(2 downto 0);
signal CompressorOut_bh57_53_53 :  std_logic_vector(1 downto 0);
signal heap_bh57_w8_21, heap_bh57_w8_21_d1 :  std_logic;
signal heap_bh57_w9_18, heap_bh57_w9_18_d1 :  std_logic;
signal CompressorIn_bh57_54_83 :  std_logic_vector(2 downto 0);
signal CompressorIn_bh57_54_84 :  std_logic_vector(1 downto 0);
signal CompressorOut_bh57_54_54 :  std_logic_vector(2 downto 0);
signal heap_bh57_w11_18, heap_bh57_w11_18_d1 :  std_logic;
signal heap_bh57_w12_16, heap_bh57_w12_16_d1 :  std_logic;
signal heap_bh57_w13_14 :  std_logic;
signal CompressorIn_bh57_55_85 :  std_logic_vector(2 downto 0);
signal CompressorIn_bh57_55_86 :  std_logic_vector(1 downto 0);
signal CompressorOut_bh57_55_55 :  std_logic_vector(2 downto 0);
signal heap_bh57_w18_8, heap_bh57_w18_8_d1 :  std_logic;
signal heap_bh57_w19_6, heap_bh57_w19_6_d1 :  std_logic;
signal heap_bh57_w20_6, heap_bh57_w20_6_d1 :  std_logic;
signal CompressorIn_bh57_56_87 :  std_logic_vector(2 downto 0);
signal CompressorIn_bh57_56_88 :  std_logic_vector(1 downto 0);
signal CompressorOut_bh57_56_56 :  std_logic_vector(2 downto 0);
signal heap_bh57_w13_15, heap_bh57_w13_15_d1 :  std_logic;
signal heap_bh57_w14_15, heap_bh57_w14_15_d1 :  std_logic;
signal heap_bh57_w15_11, heap_bh57_w15_11_d1 :  std_logic;
signal finalAdderIn0_bh57 :  std_logic_vector(23 downto 0);
signal finalAdderIn1_bh57 :  std_logic_vector(23 downto 0);
signal finalAdderCin_bh57 :  std_logic;
signal finalAdderOut_bh57 :  std_logic_vector(23 downto 0);
signal CompressionResult57 :  std_logic_vector(24 downto 0);
attribute rom_extract: string;
attribute rom_style: string;
attribute rom_extract of SmallMultTableP3x3r6XuYu: component is "yes";
attribute rom_style of SmallMultTableP3x3r6XuYu: component is "distributed";
begin
   process(clk)
      begin
         if clk'event and clk = '1' then
            heap_bh57_w22_0_d1 <=  heap_bh57_w22_0;
            heap_bh57_w23_0_d1 <=  heap_bh57_w23_0;
            heap_bh57_w1_9_d1 <=  heap_bh57_w1_9;
            heap_bh57_w5_17_d1 <=  heap_bh57_w5_17;
            heap_bh57_w7_17_d1 <=  heap_bh57_w7_17;
            heap_bh57_w1_12_d1 <=  heap_bh57_w1_12;
            tempR_bh57_0_d1 <=  tempR_bh57_0;
            heap_bh57_w9_17_d1 <=  heap_bh57_w9_17;
            heap_bh57_w10_17_d1 <=  heap_bh57_w10_17;
            heap_bh57_w2_15_d1 <=  heap_bh57_w2_15;
            heap_bh57_w3_17_d1 <=  heap_bh57_w3_17;
            heap_bh57_w4_20_d1 <=  heap_bh57_w4_20;
            heap_bh57_w4_21_d1 <=  heap_bh57_w4_21;
            heap_bh57_w5_20_d1 <=  heap_bh57_w5_20;
            heap_bh57_w6_20_d1 <=  heap_bh57_w6_20;
            heap_bh57_w6_21_d1 <=  heap_bh57_w6_21;
            heap_bh57_w7_20_d1 <=  heap_bh57_w7_20;
            heap_bh57_w8_20_d1 <=  heap_bh57_w8_20;
            heap_bh57_w10_18_d1 <=  heap_bh57_w10_18;
            heap_bh57_w15_10_d1 <=  heap_bh57_w15_10;
            heap_bh57_w16_10_d1 <=  heap_bh57_w16_10;
            heap_bh57_w16_11_d1 <=  heap_bh57_w16_11;
            heap_bh57_w17_10_d1 <=  heap_bh57_w17_10;
            heap_bh57_w20_5_d1 <=  heap_bh57_w20_5;
            heap_bh57_w21_2_d1 <=  heap_bh57_w21_2;
            heap_bh57_w22_1_d1 <=  heap_bh57_w22_1;
            heap_bh57_w8_21_d1 <=  heap_bh57_w8_21;
            heap_bh57_w9_18_d1 <=  heap_bh57_w9_18;
            heap_bh57_w11_18_d1 <=  heap_bh57_w11_18;
            heap_bh57_w12_16_d1 <=  heap_bh57_w12_16;
            heap_bh57_w18_8_d1 <=  heap_bh57_w18_8;
            heap_bh57_w19_6_d1 <=  heap_bh57_w19_6;
            heap_bh57_w20_6_d1 <=  heap_bh57_w20_6;
            heap_bh57_w13_15_d1 <=  heap_bh57_w13_15;
            heap_bh57_w14_15_d1 <=  heap_bh57_w14_15;
            heap_bh57_w15_11_d1 <=  heap_bh57_w15_11;
         end if;
      end process;
   XX_m56 <= Y ;
   YY_m56 <= X ;
   -- code generated by IntMultiplier::buildHeapLogicOnly()
   -- buildheaplogiconly called for lsbX=0 lsbY=0 msbX=18 msbY=17
   Xp_m56b58 <= XX_m56(17 downto 0) & "";
   Yp_m56b58 <= YY_m56(16 downto 0) & "0";
   x_m56b58_0 <= Xp_m56b58(2 downto 0);
   x_m56b58_1 <= Xp_m56b58(5 downto 3);
   x_m56b58_2 <= Xp_m56b58(8 downto 6);
   x_m56b58_3 <= Xp_m56b58(11 downto 9);
   x_m56b58_4 <= Xp_m56b58(14 downto 12);
   x_m56b58_5 <= Xp_m56b58(17 downto 15);
   y_m56b58_0 <= Yp_m56b58(2 downto 0);
   y_m56b58_1 <= Yp_m56b58(5 downto 3);
   y_m56b58_2 <= Yp_m56b58(8 downto 6);
   y_m56b58_3 <= Yp_m56b58(11 downto 9);
   y_m56b58_4 <= Yp_m56b58(14 downto 12);
   y_m56b58_5 <= Yp_m56b58(17 downto 15);
   ----------------Synchro barrier, entering cycle 0----------------
   -- Partial product row number 0
   Y0X3_58_m56 <= y_m56b58_0 & x_m56b58_3;
   PP_m56_58X3Y0_Tbl: SmallMultTableP3x3r6XuYu  -- pipelineDepth=0 maxInDelay=0
      port map ( clk  => clk,
                 rst  => rst,
                 X => Y0X3_58_m56,
                 Y => PP58X3Y0_m56);
   -- Adding the relevant bits to the heap of bits
   heap_bh57_w0_0 <= PP58X3Y0_m56(3); -- cycle= 0 cp= 5.7432e-10
   heap_bh57_w1_0 <= PP58X3Y0_m56(4); -- cycle= 0 cp= 5.7432e-10
   heap_bh57_w2_0 <= PP58X3Y0_m56(5); -- cycle= 0 cp= 5.7432e-10

   Y0X4_58_m56 <= y_m56b58_0 & x_m56b58_4;
   PP_m56_58X4Y0_Tbl: SmallMultTableP3x3r6XuYu  -- pipelineDepth=0 maxInDelay=0
      port map ( clk  => clk,
                 rst  => rst,
                 X => Y0X4_58_m56,
                 Y => PP58X4Y0_m56);
   -- Adding the relevant bits to the heap of bits
   heap_bh57_w1_1 <= PP58X4Y0_m56(1); -- cycle= 0 cp= 5.7432e-10
   heap_bh57_w2_1 <= PP58X4Y0_m56(2); -- cycle= 0 cp= 5.7432e-10
   heap_bh57_w3_0 <= PP58X4Y0_m56(3); -- cycle= 0 cp= 5.7432e-10
   heap_bh57_w4_0 <= PP58X4Y0_m56(4); -- cycle= 0 cp= 5.7432e-10
   heap_bh57_w5_0 <= PP58X4Y0_m56(5); -- cycle= 0 cp= 5.7432e-10

   Y0X5_58_m56 <= y_m56b58_0 & x_m56b58_5;
   PP_m56_58X5Y0_Tbl: SmallMultTableP3x3r6XuYu  -- pipelineDepth=0 maxInDelay=0
      port map ( clk  => clk,
                 rst  => rst,
                 X => Y0X5_58_m56,
                 Y => PP58X5Y0_m56);
   -- Adding the relevant bits to the heap of bits
   heap_bh57_w4_1 <= PP58X5Y0_m56(1); -- cycle= 0 cp= 5.7432e-10
   heap_bh57_w5_1 <= PP58X5Y0_m56(2); -- cycle= 0 cp= 5.7432e-10
   heap_bh57_w6_0 <= PP58X5Y0_m56(3); -- cycle= 0 cp= 5.7432e-10
   heap_bh57_w7_0 <= PP58X5Y0_m56(4); -- cycle= 0 cp= 5.7432e-10
   heap_bh57_w8_0 <= PP58X5Y0_m56(5); -- cycle= 0 cp= 5.7432e-10

   -- Partial product row number 1
   Y1X2_58_m56 <= y_m56b58_1 & x_m56b58_2;
   PP_m56_58X2Y1_Tbl: SmallMultTableP3x3r6XuYu  -- pipelineDepth=0 maxInDelay=0
      port map ( clk  => clk,
                 rst  => rst,
                 X => Y1X2_58_m56,
                 Y => PP58X2Y1_m56);
   -- Adding the relevant bits to the heap of bits
   heap_bh57_w0_1 <= PP58X2Y1_m56(3); -- cycle= 0 cp= 5.7432e-10
   heap_bh57_w1_2 <= PP58X2Y1_m56(4); -- cycle= 0 cp= 5.7432e-10
   heap_bh57_w2_2 <= PP58X2Y1_m56(5); -- cycle= 0 cp= 5.7432e-10

   Y1X3_58_m56 <= y_m56b58_1 & x_m56b58_3;
   PP_m56_58X3Y1_Tbl: SmallMultTableP3x3r6XuYu  -- pipelineDepth=0 maxInDelay=0
      port map ( clk  => clk,
                 rst  => rst,
                 X => Y1X3_58_m56,
                 Y => PP58X3Y1_m56);
   -- Adding the relevant bits to the heap of bits
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
                 X1 => CompressorIn_bh57_21_27);
   heap_bh57_w16_7 <= CompressorOut_bh57_21_21(0); -- cycle= 0 cp= 1.10504e-09
   heap_bh57_w17_6 <= CompressorOut_bh57_21_21(1); -- cycle= 0 cp= 1.10504e-09
   heap_bh57_w18_3 <= CompressorOut_bh57_21_21(2); -- cycle= 0 cp= 1.10504e-09

   ----------------Synchro barrier, entering cycle 0----------------
   CompressorIn_bh57_22_28 <= heap_bh57_w17_3 & heap_bh57_w17_2 & heap_bh57_w17_1 & heap_bh57_w17_0;
   CompressorIn_bh57_22_29(0) <= heap_bh57_w18_2;
   Compressor_bh57_22: Compressor_14_3_d
      port map ( R => CompressorOut_bh57_22_22   ,
                 X0 => CompressorIn_bh57_22_28,
                 X1 => CompressorIn_bh57_22_29);
   heap_bh57_w17_7 <= CompressorOut_bh57_22_22(0); -- cycle= 0 cp= 1.10504e-09
   heap_bh57_w18_4 <= CompressorOut_bh57_22_22(1); -- cycle= 0 cp= 1.10504e-09
   heap_bh57_w19_3 <= CompressorOut_bh57_22_22(2); -- cycle= 0 cp= 1.10504e-09

   ----------------Synchro barrier, entering cycle 0----------------
   CompressorIn_bh57_23_30 <= heap_bh57_w3_3 & heap_bh57_w3_2 & heap_bh57_w3_1 & heap_bh57_w3_0;
   Compressor_bh57_23: Compressor_4_3_e
      port map ( R => CompressorOut_bh57_23_23   ,
                 X0 => CompressorIn_bh57_23_30);
   heap_bh57_w3_13 <= CompressorOut_bh57_23_23(0); -- cycle= 0 cp= 1.10504e-09
   heap_bh57_w4_16 <= CompressorOut_bh57_23_23(1); -- cycle= 0 cp= 1.10504e-09
   heap_bh57_w5_16 <= CompressorOut_bh57_23_23(2); -- cycle= 0 cp= 1.10504e-09

   ----------------Synchro barrier, entering cycle 0----------------
   CompressorIn_bh57_24_31 <= heap_bh57_w1_2 & heap_bh57_w1_1 & heap_bh57_w1_0;
   CompressorIn_bh57_24_32 <= heap_bh57_w2_2 & heap_bh57_w2_1;
   Compressor_bh57_24: Compressor_23_3_f
      port map ( R => CompressorOut_bh57_24_24   ,
                 X0 => CompressorIn_bh57_24_31,
                 X1 => CompressorIn_bh57_24_32);
   heap_bh57_w1_11 <= CompressorOut_bh57_24_24(0); -- cycle= 0 cp= 1.10504e-09
   heap_bh57_w2_12 <= CompressorOut_bh57_24_24(1); -- cycle= 0 cp= 1.10504e-09
   heap_bh57_w3_14 <= CompressorOut_bh57_24_24(2); -- cycle= 0 cp= 1.10504e-09

   ----------------Synchro barrier, entering cycle 0----------------
   CompressorIn_bh57_25_33 <= heap_bh57_w10_2 & heap_bh57_w10_1 & heap_bh57_w10_0;
   CompressorIn_bh57_25_34 <= heap_bh57_w11_2 & heap_bh57_w11_1;
   Compressor_bh57_25: Compressor_23_3_f
      port map ( R => CompressorOut_bh57_25_25   ,
                 X0 => CompressorIn_bh57_25_33,
                 X1 => CompressorIn_bh57_25_34);
   heap_bh57_w10_13 <= CompressorOut_bh57_25_25(0); -- cycle= 0 cp= 1.10504e-09
   heap_bh57_w11_12 <= CompressorOut_bh57_25_25(1); -- cycle= 0 cp= 1.10504e-09
   heap_bh57_w12_10 <= CompressorOut_bh57_25_25(2); -- cycle= 0 cp= 1.10504e-09

   ----------------Synchro barrier, entering cycle 0----------------
   CompressorIn_bh57_26_35 <= heap_bh57_w19_2 & heap_bh57_w19_1 & heap_bh57_w19_0;
   CompressorIn_bh57_26_36 <= heap_bh57_w20_2 & heap_bh57_w20_1;
   Compressor_bh57_26: Compressor_23_3_f
      port map ( R => CompressorOut_bh57_26_26   ,
                 X0 => CompressorIn_bh57_26_35,
                 X1 => CompressorIn_bh57_26_36);
   heap_bh57_w19_4 <= CompressorOut_bh57_26_26(0); -- cycle= 0 cp= 1.10504e-09
   heap_bh57_w20_3 <= CompressorOut_bh57_26_26(1); -- cycle= 0 cp= 1.10504e-09
   heap_bh57_w21_1 <= CompressorOut_bh57_26_26(2); -- cycle= 0 cp= 1.10504e-09

   ----------------Synchro barrier, entering cycle 0----------------
   CompressorIn_bh57_27_37 <= heap_bh57_w5_0 & heap_bh57_w5_16 & heap_bh57_w5_15 & heap_bh57_w5_14 & heap_bh57_w5_13 & heap_bh57_w5_12;
   Compressor_bh57_27: Compressor_6_3_c
      port map ( R => CompressorOut_bh57_27_27   ,
                 X0 => CompressorIn_bh57_27_37);
   heap_bh57_w5_17 <= CompressorOut_bh57_27_27(0); -- cycle= 0 cp= 1.63576e-09
   heap_bh57_w6_17 <= CompressorOut_bh57_27_27(1); -- cycle= 0 cp= 1.63576e-09
   heap_bh57_w7_17 <= CompressorOut_bh57_27_27(2); -- cycle= 0 cp= 1.63576e-09

   ----------------Synchro barrier, entering cycle 0----------------
   CompressorIn_bh57_28_38 <= heap_bh57_w6_16 & heap_bh57_w6_15 & heap_bh57_w6_14 & heap_bh57_w6_13 & heap_bh57_w6_12 & heap_bh57_w6_11;
   Compressor_bh57_28: Compressor_6_3_c
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
                 X1 => CompressorIn_bh57_34_47);
   heap_bh57_w4_19 <= CompressorOut_bh57_34_34(0); -- cycle= 0 cp= 1.63576e-09
   heap_bh57_w5_19 <= CompressorOut_bh57_34_34(1); -- cycle= 0 cp= 1.63576e-09
   heap_bh57_w6_19 <= CompressorOut_bh57_34_34(2); -- cycle= 0 cp= 1.63576e-09
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
