kuanwoo/SYMPL64_FloatingPoint_RISC-/FloPoCo_operators/Log_Clk9.vhdl

-- vagrant@vagrant-ubuntu-trusty-32:~/flopoco-3.0.beta5$ ./flopoco -name=Log_Clk -frequency=200 -useHardMult=no FPLog 9 23 0
-- Updating entity name to: Log_Clk
-- 
-- Final report:
-- |---Entity LZOC_23_5_uid3
-- |      Pipeline depth = 1
-- |---Entity LeftShifter_12_by_max_12_uid6
-- |      Not pipelined
-- |---Entity InvTable_0_9_10
-- |      Not pipelined
-- |---Entity IntAdder_27_f200_uid11
-- |      Not pipelined
-- |---Entity IntAdder_27_f200_uid18
-- |      Not pipelined
-- |---Entity IntSquarer_16_uid25
-- |      Pipeline depth = 1
-- |---Entity IntAdder_27_f200_uid28
-- |      Not pipelined
-- |---Entity LogTable_0_9_40
-- |      Not pipelined
-- |---Entity LogTable_1_7_33
-- |      Not pipelined
-- |---Entity IntAdder_40_f200_uid45
-- |      Not pipelined
-- |---Entity IntAdder_40_f200_uid52
-- |      Not pipelined
-- |   |---Entity KCMTable_6_93032640_unsigned
-- |   |      Not pipelined
-- |   |---Entity KCMTable_3_93032640_unsigned
-- |   |      Not pipelined
-- |   |---Entity IntAdder_30_f200_uid64
-- |   |      Not pipelined
-- |---Entity IntIntKCM_9_93032640_unsigned
-- |      Not pipelined
-- |---Entity IntAdder_49_f200_uid72
-- |      Not pipelined
-- |---Entity LZCShifter_49_to_40_counting_64_uid79
-- |      Pipeline depth = 2
-- |---Entity RightShifter_16_by_max_15_uid82
-- |      Not pipelined
-- |---Entity IntAdder_29_f200_uid85
-- |      Not pipelined
-- |---Entity IntAdder_32_f200_uid92
-- |      Not pipelined
-- Entity Log_Clk
--    Pipeline depth = 8
-- Output file: flopoco.vhdl
--------------------------------------------------------------------------------
--                               LZOC_23_5_uid3
-- This operator is part of the Infinite Virtual Library FloPoCoLib
-- All rights reserved
-- Authors:
--------------------------------------------------------------------------------
-- Pipeline depth: 1 cycles

library ieee;
use ieee.std_logic_1164.all;
use ieee.std_logic_arith.all;
use ieee.std_logic_unsigned.all;
library std;
use std.textio.all;
library work;

entity LZOC_23_5_uid3 is
   port ( clk, rst : in std_logic;
          I : in  std_logic_vector(22 downto 0);
          OZB : in  std_logic;
          O : out  std_logic_vector(4 downto 0)   );
end entity;

architecture arch of LZOC_23_5_uid3 is
signal sozb, sozb_d1 :  std_logic;
signal level5 :  std_logic_vector(31 downto 0);
signal digit5, digit5_d1 :  std_logic;
signal level4 :  std_logic_vector(15 downto 0);
signal digit4, digit4_d1 :  std_logic;
signal level3, level3_d1 :  std_logic_vector(7 downto 0);
signal digit3, digit3_d1 :  std_logic;
signal level2 :  std_logic_vector(3 downto 0);
signal digit2 :  std_logic;
signal level1 :  std_logic_vector(1 downto 0);
signal digit1 :  std_logic;
begin
   process(clk)
      begin
         if clk'event and clk = '1' then
            sozb_d1 <=  sozb;
            digit5_d1 <=  digit5;
            digit4_d1 <=  digit4;
            level3_d1 <=  level3;
            digit3_d1 <=  digit3;
         end if;
      end process;
   sozb <= OZB;
   level5<= I& (8 downto 0 => not(sozb));
   digit5<= '1' when level5(31 downto 16) = (31 downto 16 => sozb) else '0';
   level4<= level5(15 downto 0) when digit5='1' else level5(31 downto 16);
   digit4<= '1' when level4(15 downto 8) = (15 downto 8 => sozb) else '0';
   level3<= level4(7 downto 0) when digit4='1' else level4(15 downto 8);
   digit3<= '1' when level3(7 downto 4) = (7 downto 4 => sozb) else '0';
   ----------------Synchro barrier, entering cycle 1----------------
   level2<= level3_d1(3 downto 0) when digit3_d1='1' else level3_d1(7 downto 4);
   digit2<= '1' when level2(3 downto 2) = (3 downto 2 => sozb_d1) else '0';
   level1<= level2(1 downto 0) when digit2='1' else level2(3 downto 2);
   digit1<= '1' when level1(1 downto 1) = (1 downto 1 => sozb_d1) else '0';
   O <= digit5_d1 & digit4_d1 & digit3_d1 & digit2 & digit1;
end architecture;

--------------------------------------------------------------------------------
--                       LeftShifter_12_by_max_12_uid6
-- This operator is part of the Infinite Virtual Library FloPoCoLib
-- All rights reserved
-- Authors: Bogdan Pasca, Florent de Dinechin (2008-2011)
--------------------------------------------------------------------------------
-- Pipeline depth: 0 cycles

library ieee;
use ieee.std_logic_1164.all;
use ieee.std_logic_arith.all;
use ieee.std_logic_unsigned.all;
library std;
use std.textio.all;
library work;

entity LeftShifter_12_by_max_12_uid6 is
   port ( clk, rst : in std_logic;
          X : in  std_logic_vector(11 downto 0);
          S : in  std_logic_vector(3 downto 0);
          R : out  std_logic_vector(23 downto 0)   );
end entity;

architecture arch of LeftShifter_12_by_max_12_uid6 is
signal level0 :  std_logic_vector(11 downto 0);
signal ps :  std_logic_vector(3 downto 0);
signal level1 :  std_logic_vector(12 downto 0);
signal level2 :  std_logic_vector(14 downto 0);
signal level3 :  std_logic_vector(18 downto 0);
signal level4 :  std_logic_vector(26 downto 0);
begin
   process(clk)
      begin
         if clk'event and clk = '1' then
         end if;
      end process;
   level0<= X;
   ps<= S;
   level1<= level0 & (0 downto 0 => '0') when ps(0)= '1' else     (0 downto 0 => '0') & level0;
   level2<= level1 & (1 downto 0 => '0') when ps(1)= '1' else     (1 downto 0 => '0') & level1;
   level3<= level2 & (3 downto 0 => '0') when ps(2)= '1' else     (3 downto 0 => '0') & level2;
   level4<= level3 & (7 downto 0 => '0') when ps(3)= '1' else     (7 downto 0 => '0') & level3;
   R <= level4(23 downto 0);
end architecture;

--------------------------------------------------------------------------------
--                              InvTable_0_9_10
-- This operator is part of the Infinite Virtual Library FloPoCoLib
-- All rights reserved
-- Authors: Florent de Dinechin (2007-2012)
--------------------------------------------------------------------------------
library ieee;
use ieee.std_logic_1164.all;
use ieee.numeric_std.all;
library work;
entity InvTable_0_9_10 is
   port ( clk, rst : in std_logic;
          X : in  std_logic_vector(8 downto 0);
          Y : out  std_logic_vector(9 downto 0)   );
end entity;

architecture arch of InvTable_0_9_10 is
begin
  with X select  Y <=
   "1000000000" when "000000000",
   "1000000000" when "000000001",
   "0111111111" when "000000010",
   "0111111110" when "000000011",
   "0111111101" when "000000100",
   "0111111100" when "000000101",
   "0111111011" when "000000110",
   "0111111010" when "000000111",
   "0111111001" when "000001000",
   "0111111000" when "000001001",
   "0111110111" when "000001010",
   "0111110110" when "000001011",
   "0111110101" when "000001100",
   "0111110100" when "000001101",
   "0111110011" when "000001110",
   "0111110010" when "000001111",
   "0111110001" when "000010000",
   "0111110000" when "000010001",
   "0111101111" when "000010010",
   "0111101110" when "000010011",
   "0111101101" when "000010100",
   "0111101100" when "000010101",
   "0111101011" when "000010110",
   "0111101010" when "000010111",
   "0111101010" when "000011000",
   "0111101001" when "000011001",
   "0111101000" when "000011010",
   "0111100111" when "000011011",
   "0111100110" when "000011100",
   "0111100101" when "000011101",
   "0111100100" when "000011110",
   "0111100011" when "000011111",
   "0111100010" when "000100000",
   "0111100001" when "000100001",
   "0111100001" when "000100010",
   "0111100000" when "000100011",
   "0111011111" when "000100100",
   "0111011110" when "000100101",
   "0111011101" when "000100110",
   "0111011100" when "000100111",
   "0111011011" when "000101000",
   "0111011011" when "000101001",
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
   "1000000100" when "111111001",
   "1000000100" when "111111010",
   "1000000011" when "111111011",
   "1000000011" when "111111100",
   "1000000010" when "111111101",
   "1000000010" when "111111110",
   "1000000001" when "111111111",
   "----------" when others;
end architecture;

--------------------------------------------------------------------------------
--                           IntAdder_27_f200_uid11
--                    (IntAdderAlternative_27_f200_uid15)
-- This operator is part of the Infinite Virtual Library FloPoCoLib
-- All rights reserved
-- Authors: Bogdan Pasca, Florent de Dinechin (2008-2010)
--------------------------------------------------------------------------------
-- Pipeline depth: 0 cycles

library ieee;
use ieee.std_logic_1164.all;
use ieee.std_logic_arith.all;
use ieee.std_logic_unsigned.all;
library std;
use std.textio.all;
library work;

entity IntAdder_27_f200_uid11 is
   port ( clk, rst : in std_logic;
          X : in  std_logic_vector(26 downto 0);
          Y : in  std_logic_vector(26 downto 0);
          Cin : in  std_logic;
          R : out  std_logic_vector(26 downto 0)   );
end entity;

architecture arch of IntAdder_27_f200_uid11 is
begin
   process(clk)
      begin
         if clk'event and clk = '1' then
         end if;
      end process;
   --Alternative
    R <= X + Y + Cin;
end architecture;

--------------------------------------------------------------------------------
--                           IntAdder_27_f200_uid18
--                    (IntAdderAlternative_27_f200_uid22)
-- This operator is part of the Infinite Virtual Library FloPoCoLib
-- All rights reserved
-- Authors: Bogdan Pasca, Florent de Dinechin (2008-2010)
--------------------------------------------------------------------------------
-- Pipeline depth: 0 cycles

library ieee;
use ieee.std_logic_1164.all;
use ieee.std_logic_arith.all;
use ieee.std_logic_unsigned.all;
library std;
use std.textio.all;
library work;

entity IntAdder_27_f200_uid18 is
   port ( clk, rst : in std_logic;
          X : in  std_logic_vector(26 downto 0);
          Y : in  std_logic_vector(26 downto 0);
          Cin : in  std_logic;
          R : out  std_logic_vector(26 downto 0)   );
end entity;

architecture arch of IntAdder_27_f200_uid18 is
begin
   process(clk)
      begin
         if clk'event and clk = '1' then
         end if;
      end process;
   --Alternative
    R <= X + Y + Cin;
end architecture;

--------------------------------------------------------------------------------
--                            IntSquarer_16_uid25
-- This operator is part of the Infinite Virtual Library FloPoCoLib
-- All rights reserved
-- Authors: Bogdan Pasca (2009)
--------------------------------------------------------------------------------
-- Pipeline depth: 1 cycles

library ieee;
use ieee.std_logic_1164.all;
use ieee.std_logic_arith.all;
use ieee.std_logic_unsigned.all;
library work;
entity IntSquarer_16_uid25 is
   port ( clk, rst : in std_logic;
          X : in  std_logic_vector(15 downto 0);
          R : out  std_logic_vector(31 downto 0)   );
end entity;

architecture arch of IntSquarer_16_uid25 is
signal sX, sX_d1 :  std_logic_vector(15 downto 0);
signal sY, sY_d1 :  std_logic_vector(15 downto 0);
begin
   process(clk)
      begin
         if clk'event and clk = '1' then
            sX_d1 <=  sX;
            sY_d1 <=  sY;
         end if;
      end process;
   sX <= X;
   sY <= X;
   ----------------Synchro barrier, entering cycle 1----------------
   R <= sX_d1 * sY_d1;
end architecture;

--------------------------------------------------------------------------------
--                           IntAdder_27_f200_uid28
--                    (IntAdderAlternative_27_f200_uid32)
-- This operator is part of the Infinite Virtual Library FloPoCoLib
-- All rights reserved
-- Authors: Bogdan Pasca, Florent de Dinechin (2008-2010)
--------------------------------------------------------------------------------
-- Pipeline depth: 0 cycles

library ieee;
use ieee.std_logic_1164.all;
use ieee.std_logic_arith.all;
use ieee.std_logic_unsigned.all;
library std;
use std.textio.all;
library work;

entity IntAdder_27_f200_uid28 is
   port ( clk, rst : in std_logic;
          X : in  std_logic_vector(26 downto 0);
          Y : in  std_logic_vector(26 downto 0);
          Cin : in  std_logic;
          R : out  std_logic_vector(26 downto 0)   );
end entity;

architecture arch of IntAdder_27_f200_uid28 is
begin
   process(clk)
      begin
         if clk'event and clk = '1' then
         end if;
      end process;
   --Alternative
    R <= X + Y + Cin;
end architecture;

--------------------------------------------------------------------------------
--                              LogTable_0_9_40
-- This operator is part of the Infinite Virtual Library FloPoCoLib
-- All rights reserved
-- Authors: Florent de Dinechin (2007-2012)
--------------------------------------------------------------------------------
library ieee;
use ieee.std_logic_1164.all;
use ieee.numeric_std.all;
library work;
entity LogTable_0_9_40 is
   port ( clk, rst : in std_logic;
          X : in  std_logic_vector(8 downto 0);
          Y : out  std_logic_vector(39 downto 0)   );
end entity;

architecture arch of LogTable_0_9_40 is
   -- Build a 2-D array type for the RoM
   subtype word_t is std_logic_vector(39 downto 0);
   type memory_t is array(0 to 511) of word_t;
   function init_rom
      return memory_t is
      variable tmp : memory_t := (
   "1111111111111100000000000000000000000000",
   "1111111111111100000000000000000000000000",
   "0000000001111100001000000000101010101111",
   "0000000011111100100000000101010110010110",
   "0000000101111101001000010010000101000110",
   "0000000111111110000000101010111010110001",
   "0000001001111111001001010011111100101101",
   "0000001100000000100010010001010001110001",
   "0000001110000010001011100111000010011001",
   "0000010000000100000101011001011000100101",
   "0000010010000110001111101100011111111011",
   "0000010100001000101010100100100101100110",
   "0000010110001011010110000101111000011010",
   "0000011000001110010010010100101000110010",
   "0000011010010001011111010101001000110001",
   "0000011100010100111101001011101100000101",
   "0000011110011000101011111100101000000101",
   "0000100000011100101011101100010011110100",
   "0000100010100000111100011111001000000000",
   "0000100100100101011110011001011111000111",
   "0000100110101010010001011111110101010001",
   "0000101000101111010101110110101000010111",
   "0000101010110100101011100010011000000010",
   "0000101100111010010010100111100101101010",
   "0000101100111010010010100111100101101010",
   "0000101111000000001011001010110100011011",
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
          R : out  std_logic_vector(39 downto 0)   );
end entity;

architecture arch of IntAdder_40_f200_uid45 is
begin
   process(clk)
      begin
         if clk'event and clk = '1' then
         end if;
      end process;
   --Alternative
    R <= X + Y + Cin;
end architecture;

--------------------------------------------------------------------------------
--                           IntAdder_40_f200_uid52
--                    (IntAdderAlternative_40_f200_uid56)
-- This operator is part of the Infinite Virtual Library FloPoCoLib
-- All rights reserved
-- Authors: Bogdan Pasca, Florent de Dinechin (2008-2010)
--------------------------------------------------------------------------------
-- Pipeline depth: 0 cycles

library ieee;
use ieee.std_logic_1164.all;
use ieee.std_logic_arith.all;
use ieee.std_logic_unsigned.all;
library std;
use std.textio.all;
library work;

entity IntAdder_40_f200_uid52 is
   port ( clk, rst : in std_logic;
          X : in  std_logic_vector(39 downto 0);
          Y : in  std_logic_vector(39 downto 0);
          Cin : in  std_logic;
          R : out  std_logic_vector(39 downto 0)   );
end entity;

architecture arch of IntAdder_40_f200_uid52 is
begin
   process(clk)
      begin
         if clk'event and clk = '1' then
         end if;
      end process;
   --Alternative
    R <= X + Y + Cin;
end architecture;

--------------------------------------------------------------------------------
--                        KCMTable_6_93032640_unsigned
-- This operator is part of the Infinite Virtual Library FloPoCoLib
-- All rights reserved
-- Authors: Florent de Dinechin (2007-2012)
--------------------------------------------------------------------------------
library ieee;
use ieee.std_logic_1164.all;
use ieee.numeric_std.all;
library work;
entity KCMTable_6_93032640_unsigned is
   port ( clk, rst : in std_logic;
          X : in  std_logic_vector(5 downto 0);
          Y : out  std_logic_vector(32 downto 0)   );
end entity;

architecture arch of KCMTable_6_93032640_unsigned is
begin
  with X select  Y <=
   "000000000000000000000000000000000" when "000000",
   "000000101100010111001000011000000" when "000001",
   "000001011000101110010000110000000" when "000010",
   "000010000101000101011001001000000" when "000011",
   "000010110001011100100001100000000" when "000100",
   "000011011101110011101001111000000" when "000101",
   "000100001010001010110010010000000" when "000110",
   "000100110110100001111010101000000" when "000111",
   "000101100010111001000011000000000" when "001000",
   "000110001111010000001011011000000" when "001001",
   "000110111011100111010011110000000" when "001010",
   "000111100111111110011100001000000" when "001011",
   "001000010100010101100100100000000" when "001100",
   "001001000000101100101100111000000" when "001101",
   "001001101101000011110101010000000" when "001110",
   "001010011001011010111101101000000" when "001111",
   "001011000101110010000110000000000" when "010000",
   "001011110010001001001110011000000" when "010001",
   "001100011110100000010110110000000" when "010010",
   "001101001010110111011111001000000" when "010011",
   "001101110111001110100111100000000" when "010100",
   "001110100011100101101111111000000" when "010101",
   "001111001111111100111000010000000" when "010110",
   "001111111100010100000000101000000" when "010111",
   "010000101000101011001001000000000" when "011000",
   "010001010101000010010001011000000" when "011001",
   "010010000001011001011001110000000" when "011010",
   "010010101101110000100010001000000" when "011011",
   "010011011010000111101010100000000" when "011100",
   "010100000110011110110010111000000" when "011101",
   "010100110010110101111011010000000" when "011110",
   "010101011111001101000011101000000" when "011111",
   "010110001011100100001100000000000" when "100000",
   "010110110111111011010100011000000" when "100001",
   "010111100100010010011100110000000" when "100010",
   "011000010000101001100101001000000" when "100011",
   "011000111101000000101101100000000" when "100100",
   "011001101001010111110101111000000" when "100101",
   "011010010101101110111110010000000" when "100110",
   "011011000010000110000110101000000" when "100111",
   "011011101110011101001111000000000" when "101000",
   "011100011010110100010111011000000" when "101001",
   "011101000111001011011111110000000" when "101010",
   "011101110011100010101000001000000" when "101011",
   "011110011111111001110000100000000" when "101100",
   "011111001100010000111000111000000" when "101101",
   "011111111000101000000001010000000" when "101110",
   "100000100100111111001001101000000" when "101111",
   "100001010001010110010010000000000" when "110000",
   "100001111101101101011010011000000" when "110001",
   "100010101010000100100010110000000" when "110010",
   "100011010110011011101011001000000" when "110011",
   "100100000010110010110011100000000" when "110100",
   "100100101111001001111011111000000" when "110101",
   "100101011011100001000100010000000" when "110110",
   "100110000111111000001100101000000" when "110111",
   "100110110100001111010101000000000" when "111000",
   "100111100000100110011101011000000" when "111001",
   "101000001100111101100101110000000" when "111010",
   "101000111001010100101110001000000" when "111011",
   "101001100101101011110110100000000" when "111100",
   "101010010010000010111110111000000" when "111101",
   "101010111110011010000111010000000" when "111110",
   "101011101010110001001111101000000" when "111111",
   "---------------------------------" when others;
end architecture;

--------------------------------------------------------------------------------
--                        KCMTable_3_93032640_unsigned
-- This operator is part of the Infinite Virtual Library FloPoCoLib
-- All rights reserved
-- Authors: Florent de Dinechin (2007-2012)
--------------------------------------------------------------------------------
library ieee;
use ieee.std_logic_1164.all;
use ieee.numeric_std.all;
library work;
entity KCMTable_3_93032640_unsigned is
   port ( clk, rst : in std_logic;
          X : in  std_logic_vector(2 downto 0);
          Y : out  std_logic_vector(29 downto 0)   );
end entity;

architecture arch of KCMTable_3_93032640_unsigned is
begin
  with X select  Y <=
   "000000000000000000000000000000" when "000",
   "000101100010111001000011000000" when "001",
   "001011000101110010000110000000" when "010",
   "010000101000101011001001000000" when "011",
   "010110001011100100001100000000" when "100",
   "011011101110011101001111000000" when "101",
   "100001010001010110010010000000" when "110",
   "100110110100001111010101000000" when "111",
   "------------------------------" when others;
end architecture;

--------------------------------------------------------------------------------
--                           IntAdder_30_f200_uid64
--                    (IntAdderAlternative_30_f200_uid68)
-- This operator is part of the Infinite Virtual Library FloPoCoLib
-- All rights reserved
-- Authors: Bogdan Pasca, Florent de Dinechin (2008-2010)
--------------------------------------------------------------------------------
-- Pipeline depth: 0 cycles

library ieee;
use ieee.std_logic_1164.all;
use ieee.std_logic_arith.all;
use ieee.std_logic_unsigned.all;
library std;
use std.textio.all;
library work;

entity IntAdder_30_f200_uid64 is
   port ( clk, rst : in std_logic;
          X : in  std_logic_vector(29 downto 0);
          Y : in  std_logic_vector(29 downto 0);
          Cin : in  std_logic;
          R : out  std_logic_vector(29 downto 0)   );
end entity;

architecture arch of IntAdder_30_f200_uid64 is
begin
   process(clk)
      begin
         if clk'event and clk = '1' then
         end if;
      end process;
   --Alternative
    R <= X + Y + Cin;
end architecture;

--------------------------------------------------------------------------------
--                       IntIntKCM_9_93032640_unsigned
-- This operator is part of the Infinite Virtual Library FloPoCoLib
-- All rights reserved
-- Authors: Bogdan Pasca, Florent de Dinechin (2009,2010)
--------------------------------------------------------------------------------
-- Pipeline depth: 0 cycles

library ieee;
use ieee.std_logic_1164.all;
use ieee.std_logic_arith.all;
use ieee.std_logic_unsigned.all;
library std;
use std.textio.all;
library work;

entity IntIntKCM_9_93032640_unsigned is
   port ( clk, rst : in std_logic;
          X : in  std_logic_vector(8 downto 0);
          R : out  std_logic_vector(35 downto 0)   );
end entity;

architecture arch of IntIntKCM_9_93032640_unsigned is
   component IntAdder_30_f200_uid64 is
      port ( clk, rst : in std_logic;
             X : in  std_logic_vector(29 downto 0);
             Y : in  std_logic_vector(29 downto 0);
             Cin : in  std_logic;
             R : out  std_logic_vector(29 downto 0)   );
   end component;

   component KCMTable_3_93032640_unsigned is
      port ( clk, rst : in std_logic;
             X : in  std_logic_vector(2 downto 0);
             Y : out  std_logic_vector(29 downto 0)   );
   end component;

   component KCMTable_6_93032640_unsigned is
      port ( clk, rst : in std_logic;
             X : in  std_logic_vector(5 downto 0);
             Y : out  std_logic_vector(32 downto 0)   );
   end component;

signal d0 :  std_logic_vector(5 downto 0);
signal pp0 :  std_logic_vector(32 downto 0);
signal d1 :  std_logic_vector(2 downto 0);
signal pp1 :  std_logic_vector(29 downto 0);
signal addOp0 :  std_logic_vector(29 downto 0);
signal addOp1 :  std_logic_vector(29 downto 0);
signal OutRes :  std_logic_vector(29 downto 0);
attribute rom_extract: string;
attribute rom_style: string;
attribute rom_extract of KCMTable_3_93032640_unsigned: component is "yes";
attribute rom_extract of KCMTable_6_93032640_unsigned: component is "yes";
attribute rom_style of KCMTable_3_93032640_unsigned: component is "distributed";
attribute rom_style of KCMTable_6_93032640_unsigned: component is "distributed";
begin
   process(clk)
      begin
         if clk'event and clk = '1' then
         end if;
      end process;
   d0 <= X(5 downto 0);
   KCMTable_0: KCMTable_6_93032640_unsigned  -- pipelineDepth=0 maxInDelay=0
      port map ( clk  => clk,
                 rst  => rst,
                 X => d0,
                 Y => pp0);
   d1 <= X(8 downto 6);
   KCMTable_1: KCMTable_3_93032640_unsigned  -- pipelineDepth=0 maxInDelay=0
      port map ( clk  => clk,
                 rst  => rst,
                 X => d1,
                 Y => pp1);
   addOp0 <= (29 downto 27 => '0') & pp0(32 downto 6) & "";
   addOp1 <= pp1(29 downto 0) & "";
   Result_Adder: IntAdder_30_f200_uid64  -- pipelineDepth=0 maxInDelay=1.22832e-09
      port map ( clk  => clk,
                 rst  => rst,
                 Cin => '0',
                 R => OutRes,
                 X => addOp0,
                 Y => addOp1);
   R <= OutRes & pp0(5 downto 0);
end architecture;

--------------------------------------------------------------------------------
--                           IntAdder_49_f200_uid72
--                    (IntAdderAlternative_49_f200_uid76)
-- This operator is part of the Infinite Virtual Library FloPoCoLib
-- All rights reserved
-- Authors: Bogdan Pasca, Florent de Dinechin (2008-2010)
--------------------------------------------------------------------------------
-- Pipeline depth: 0 cycles

library ieee;
use ieee.std_logic_1164.all;
use ieee.std_logic_arith.all;
use ieee.std_logic_unsigned.all;
library std;
use std.textio.all;
library work;

entity IntAdder_49_f200_uid72 is
   port ( clk, rst : in std_logic;
          X : in  std_logic_vector(48 downto 0);
          Y : in  std_logic_vector(48 downto 0);
          Cin : in  std_logic;
          R : out  std_logic_vector(48 downto 0)   );
end entity;

architecture arch of IntAdder_49_f200_uid72 is
begin
   process(clk)
      begin
         if clk'event and clk = '1' then
         end if;
      end process;
   --Alternative
    R <= X + Y + Cin;
end architecture;

--------------------------------------------------------------------------------
--                   LZCShifter_49_to_40_counting_64_uid79
-- This operator is part of the Infinite Virtual Library FloPoCoLib
-- All rights reserved
-- Authors: Florent de Dinechin, Bogdan Pasca (2007)
--------------------------------------------------------------------------------
-- Pipeline depth: 2 cycles

library ieee;
use ieee.std_logic_1164.all;
use ieee.std_logic_arith.all;
use ieee.std_logic_unsigned.all;
library std;
use std.textio.all;
library work;

entity LZCShifter_49_to_40_counting_64_uid79 is
   port ( clk, rst : in std_logic;
          I : in  std_logic_vector(48 downto 0);
          Count : out  std_logic_vector(5 downto 0);
          O : out  std_logic_vector(39 downto 0)   );
end entity;

architecture arch of LZCShifter_49_to_40_counting_64_uid79 is
signal level6, level6_d1 :  std_logic_vector(48 downto 0);
signal count5, count5_d1 :  std_logic;
signal level5 :  std_logic_vector(48 downto 0);
signal count4, count4_d1 :  std_logic;
signal level4 :  std_logic_vector(48 downto 0);
signal count3, count3_d1 :  std_logic;
signal level3, level3_d1 :  std_logic_vector(46 downto 0);
signal count2, count2_d1 :  std_logic;
signal level2 :  std_logic_vector(42 downto 0);
signal count1 :  std_logic;
signal level1 :  std_logic_vector(40 downto 0);
signal count0 :  std_logic;
signal level0 :  std_logic_vector(39 downto 0);
signal sCount :  std_logic_vector(5 downto 0);
begin
   process(clk)
      begin
         if clk'event and clk = '1' then
            level6_d1 <=  level6;
            count5_d1 <=  count5;
            count4_d1 <=  count4;
            count3_d1 <=  count3;
            level3_d1 <=  level3;
            count2_d1 <=  count2;
         end if;
      end process;
   level6 <= I ;
   ----------------Synchro barrier, entering cycle 1----------------
   count5<= '1' when level6_d1(48 downto 17) = (48 downto 17=>'0') else '0';
   level5<= level6_d1(48 downto 0) when count5='0' else level6_d1(16 downto 0) & (31 downto 0 => '0');

   count4<= '1' when level5(48 downto 33) = (48 downto 33=>'0') else '0';
   level4<= level5(48 downto 0) when count4='0' else level5(32 downto 0) & (15 downto 0 => '0');

   count3<= '1' when level4(48 downto 41) = (48 downto 41=>'0') else '0';
   level3<= level4(48 downto 2) when count3='0' else level4(40 downto 0) & (5 downto 0 => '0');

   count2<= '1' when level3(46 downto 43) = (46 downto 43=>'0') else '0';
   ----------------Synchro barrier, entering cycle 2----------------
   level2<= level3_d1(46 downto 4) when count2_d1='0' else level3_d1(42 downto 0);

   count1<= '1' when level2(42 downto 41) = (42 downto 41=>'0') else '0';
   level1<= level2(42 downto 2) when count1='0' else level2(40 downto 0);

   count0<= '1' when level1(40 downto 40) = (40 downto 40=>'0') else '0';
   level0<= level1(40 downto 1) when count0='0' else level1(39 downto 0);

   O <= level0;
   sCount <= count5_d1 & count4_d1 & count3_d1 & count2_d1 & count1 & count0;
   Count <= sCount;
end architecture;

--------------------------------------------------------------------------------
--                      RightShifter_16_by_max_15_uid82
-- This operator is part of the Infinite Virtual Library FloPoCoLib
-- All rights reserved
-- Authors: Bogdan Pasca, Florent de Dinechin (2008-2011)
--------------------------------------------------------------------------------
-- Pipeline depth: 0 cycles

library ieee;
use ieee.std_logic_1164.all;
use ieee.std_logic_arith.all;
use ieee.std_logic_unsigned.all;
library std;
use std.textio.all;
library work;

entity RightShifter_16_by_max_15_uid82 is
   port ( clk, rst : in std_logic;
          X : in  std_logic_vector(15 downto 0);
          S : in  std_logic_vector(3 downto 0);
          R : out  std_logic_vector(30 downto 0)   );
end entity;

architecture arch of RightShifter_16_by_max_15_uid82 is
signal level0 :  std_logic_vector(15 downto 0);
signal ps :  std_logic_vector(3 downto 0);
signal level1 :  std_logic_vector(16 downto 0);
signal level2 :  std_logic_vector(18 downto 0);
signal level3 :  std_logic_vector(22 downto 0);
signal level4 :  std_logic_vector(30 downto 0);
begin
   process(clk)
      begin
         if clk'event and clk = '1' then
         end if;
      end process;
   level0<= X;
   ps<= S;
   level1<=  (0 downto 0 => '0') & level0 when ps(0) = '1' else    level0 & (0 downto 0 => '0');
   level2<=  (1 downto 0 => '0') & level1 when ps(1) = '1' else    level1 & (1 downto 0 => '0');
   level3<=  (3 downto 0 => '0') & level2 when ps(2) = '1' else    level2 & (3 downto 0 => '0');
   level4<=  (7 downto 0 => '0') & level3 when ps(3) = '1' else    level3 & (7 downto 0 => '0');
   R <= level4(30 downto 0);
end architecture;

--------------------------------------------------------------------------------
--                           IntAdder_29_f200_uid85
--                    (IntAdderAlternative_29_f200_uid89)
-- This operator is part of the Infinite Virtual Library FloPoCoLib
-- All rights reserved
-- Authors: Bogdan Pasca, Florent de Dinechin (2008-2010)
--------------------------------------------------------------------------------
-- Pipeline depth: 0 cycles

library ieee;
use ieee.std_logic_1164.all;
use ieee.std_logic_arith.all;
use ieee.std_logic_unsigned.all;
library std;
use std.textio.all;
library work;

entity IntAdder_29_f200_uid85 is
   port ( clk, rst : in std_logic;
          X : in  std_logic_vector(28 downto 0);
          Y : in  std_logic_vector(28 downto 0);
          Cin : in  std_logic;
          R : out  std_logic_vector(28 downto 0)   );
end entity;

architecture arch of IntAdder_29_f200_uid85 is
begin
   process(clk)
      begin
         if clk'event and clk = '1' then
         end if;
      end process;
   --Alternative
    R <= X + Y + Cin;
end architecture;

--------------------------------------------------------------------------------
--                           IntAdder_32_f200_uid92
--                    (IntAdderAlternative_32_f200_uid96)
-- This operator is part of the Infinite Virtual Library FloPoCoLib
-- All rights reserved
-- Authors: Bogdan Pasca, Florent de Dinechin (2008-2010)
--------------------------------------------------------------------------------
-- Pipeline depth: 0 cycles

library ieee;
use ieee.std_logic_1164.all;
use ieee.std_logic_arith.all;
use ieee.std_logic_unsigned.all;
library std;
use std.textio.all;
library work;

entity IntAdder_32_f200_uid92 is
   port ( clk, rst : in std_logic;
          X : in  std_logic_vector(31 downto 0);
          Y : in  std_logic_vector(31 downto 0);
          Cin : in  std_logic;
          R : out  std_logic_vector(31 downto 0)   );
end entity;

architecture arch of IntAdder_32_f200_uid92 is
begin
   process(clk)
      begin
         if clk'event and clk = '1' then
         end if;
      end process;
   --Alternative
    R <= X + Y + Cin;
end architecture;

--------------------------------------------------------------------------------
--                                  Log_Clk
--                         (IterativeLog_9_23_0_200)
-- This operator is part of the Infinite Virtual Library FloPoCoLib
-- All rights reserved
-- Authors: F. de Dinechin, C. Klein  (2008-2011)
--------------------------------------------------------------------------------
-- Pipeline depth: 8 cycles

library ieee;
use ieee.std_logic_1164.all;
use ieee.std_logic_arith.all;
use ieee.std_logic_unsigned.all;
library std;
use std.textio.all;
library work;

entity Log_Clk is
   port ( clk, rst : in std_logic;
          X : in  std_logic_vector(9+23+2 downto 0);
          R : out  std_logic_vector(9+23+2 downto 0);
--- mod by JDH Sept 21, 2015 --------          
          round : buffer std_logic;
         sR_d77 : out std_logic;
          roundit : in std_logic   );
-------------------------------------          
end entity;

architecture arch of Log_Clk is
   component IntAdder_27_f200_uid11 is
      port ( clk, rst : in std_logic;
             X : in  std_logic_vector(26 downto 0);
             Y : in  std_logic_vector(26 downto 0);
             Cin : in  std_logic;
             R : out  std_logic_vector(26 downto 0)   );
   end component;

   component IntAdder_27_f200_uid18 is
      port ( clk, rst : in std_logic;
             X : in  std_logic_vector(26 downto 0);
             Y : in  std_logic_vector(26 downto 0);
             Cin : in  std_logic;
             R : out  std_logic_vector(26 downto 0)   );
   end component;

   component IntAdder_27_f200_uid28 is
      port ( clk, rst : in std_logic;
             X : in  std_logic_vector(26 downto 0);
             Y : in  std_logic_vector(26 downto 0);
             Cin : in  std_logic;
             R : out  std_logic_vector(26 downto 0)   );
   end component;

   component IntAdder_29_f200_uid85 is
      port ( clk, rst : in std_logic;
             X : in  std_logic_vector(28 downto 0);
             Y : in  std_logic_vector(28 downto 0);
             Cin : in  std_logic;
             R : out  std_logic_vector(28 downto 0)   );
   end component;

   component IntAdder_32_f200_uid92 is
      port ( clk, rst : in std_logic;
             X : in  std_logic_vector(31 downto 0);
             Y : in  std_logic_vector(31 downto 0);
             Cin : in  std_logic;
             R : out  std_logic_vector(31 downto 0)   );
   end component;

   component IntAdder_40_f200_uid45 is
      port ( clk, rst : in std_logic;
             X : in  std_logic_vector(39 downto 0);
             Y : in  std_logic_vector(39 downto 0);
             Cin : in  std_logic;
             R : out  std_logic_vector(39 downto 0)   );
   end component;

   component IntAdder_40_f200_uid52 is
      port ( clk, rst : in std_logic;
             X : in  std_logic_vector(39 downto 0);
             Y : in  std_logic_vector(39 downto 0);
             Cin : in  std_logic;
             R : out  std_logic_vector(39 downto 0)   );
   end component;

   component IntAdder_49_f200_uid72 is
      port ( clk, rst : in std_logic;
             X : in  std_logic_vector(48 downto 0);
             Y : in  std_logic_vector(48 downto 0);
             Cin : in  std_logic;
             R : out  std_logic_vector(48 downto 0)   );
   end component;

   component IntIntKCM_9_93032640_unsigned is
      port ( clk, rst : in std_logic;
             X : in  std_logic_vector(8 downto 0);
             R : out  std_logic_vector(35 downto 0)   );
   end component;

   component IntSquarer_16_uid25 is
      port ( clk, rst : in std_logic;
             X : in  std_logic_vector(15 downto 0);
             R : out  std_logic_vector(31 downto 0)   );
   end component;

   component InvTable_0_9_10 is
      port ( clk, rst : in std_logic;
             X : in  std_logic_vector(8 downto 0);
             Y : out  std_logic_vector(9 downto 0)   );
   end component;

   component LZCShifter_49_to_40_counting_64_uid79 is
      port ( clk, rst : in std_logic;
             I : in  std_logic_vector(48 downto 0);
             Count : out  std_logic_vector(5 downto 0);
             O : out  std_logic_vector(39 downto 0)   );
   end component;

   component LZOC_23_5_uid3 is
      port ( clk, rst : in std_logic;
             I : in  std_logic_vector(22 downto 0);
             OZB : in  std_logic;
             O : out  std_logic_vector(4 downto 0)   );
   end component;

   component LeftShifter_12_by_max_12_uid6 is
      port ( clk, rst : in std_logic;
             X : in  std_logic_vector(11 downto 0);
             S : in  std_logic_vector(3 downto 0);
             R : out  std_logic_vector(23 downto 0)   );
   end component;

   component LogTable_0_9_40 is
      port ( clk, rst : in std_logic;
             X : in  std_logic_vector(8 downto 0);
             Y : out  std_logic_vector(39 downto 0)   );
   end component;

   component LogTable_1_7_33 is
      port ( clk, rst : in std_logic;
             X : in  std_logic_vector(6 downto 0);
             Y : out  std_logic_vector(32 downto 0)   );
   end component;

   component RightShifter_16_by_max_15_uid82 is
      port ( clk, rst : in std_logic;
             X : in  std_logic_vector(15 downto 0);
             S : in  std_logic_vector(3 downto 0);
             R : out  std_logic_vector(30 downto 0)   );
   end component;

signal XExnSgn, XExnSgn_d1, XExnSgn_d2, XExnSgn_d3, XExnSgn_d4, XExnSgn_d5, XExnSgn_d6, XExnSgn_d7, XExnSgn_d8 :  std_logic_vector(2 downto 0);
signal FirstBit :  std_logic;
signal Y0, Y0_d1, Y0_d2 :  std_logic_vector(24 downto 0);
signal Y0h :  std_logic_vector(22 downto 0);
signal sR, sR_d1, sR_d2, sR_d3, sR_d4, sR_d5, sR_d6, sR_d7, sR_d8 :  std_logic;
signal absZ0, absZ0_d1 :  std_logic_vector(11 downto 0);
signal E :  std_logic_vector(8 downto 0);
signal absE, absE_d1, absE_d2, absE_d3, absE_d4, absE_d5, absE_d6 :  std_logic_vector(8 downto 0);
signal EeqZero, EeqZero_d1 :  std_logic;
signal lzo, lzo_d1, lzo_d2, lzo_d3, lzo_d4, lzo_d5, lzo_d6 :  std_logic_vector(4 downto 0);
signal pfinal_s :  std_logic_vector(4 downto 0);
signal shiftval :  std_logic_vector(5 downto 0);
signal shiftvalinL :  std_logic_vector(3 downto 0);
signal shiftvalinR, shiftvalinR_d1, shiftvalinR_d2, shiftvalinR_d3, shiftvalinR_d4, shiftvalinR_d5 :  std_logic_vector(3 downto 0);
signal doRR, doRR_d1, doRR_d2, doRR_d3 :  std_logic;
signal small, small_d1, small_d2, small_d3, small_d4, small_d5, small_d6, small_d7 :  std_logic;
signal small_absZ0_normd_full :  std_logic_vector(23 downto 0);
signal small_absZ0_normd, small_absZ0_normd_d1, small_absZ0_normd_d2, small_absZ0_normd_d3, small_absZ0_normd_d4, small_absZ0_normd_d5 :  std_logic_vector(11 downto 0);
signal A0, A0_d1, A0_d2, A0_d3, A0_d4, A0_d5 :  std_logic_vector(8 downto 0);
signal InvA0, InvA0_d1 :  std_logic_vector(9 downto 0);
signal P0, P0_d1 :  std_logic_vector(34 downto 0);
signal Z1 :  std_logic_vector(25 downto 0);
signal A1, A1_d1, A1_d2 :  std_logic_vector(6 downto 0);
signal B1 :  std_logic_vector(18 downto 0);
signal ZM1, ZM1_d1 :  std_logic_vector(25 downto 0);
signal P1 :  std_logic_vector(32 downto 0);
signal Y1 :  std_logic_vector(33 downto 0);
signal EiY1 :  std_logic_vector(26 downto 0);
signal addXIter1 :  std_logic_vector(26 downto 0);
signal EiYPB1, EiYPB1_d1 :  std_logic_vector(26 downto 0);
signal Pp1 :  std_logic_vector(26 downto 0);
signal Z2 :  std_logic_vector(26 downto 0);
signal Zfinal, Zfinal_d1 :  std_logic_vector(26 downto 0);
signal squarerIn :  std_logic_vector(15 downto 0);
signal Z2o2_full :  std_logic_vector(31 downto 0);
signal Z2o2_full_dummy, Z2o2_full_dummy_d1 :  std_logic_vector(31 downto 0);
signal Z2o2_normal :  std_logic_vector(12 downto 0);
signal addFinalLog1pY :  std_logic_vector(26 downto 0);
signal Log1p_normal, Log1p_normal_d1 :  std_logic_vector(26 downto 0);
signal L0 :  std_logic_vector(39 downto 0);
signal S1 :  std_logic_vector(39 downto 0);
signal L1 :  std_logic_vector(32 downto 0);
signal sopX1 :  std_logic_vector(39 downto 0);
signal S2, S2_d1 :  std_logic_vector(39 downto 0);
signal almostLog :  std_logic_vector(39 downto 0);
signal adderLogF_normalY :  std_logic_vector(39 downto 0);
signal LogF_normal :  std_logic_vector(39 downto 0);
signal absELog2 :  std_logic_vector(35 downto 0);
signal absELog2_pad :  std_logic_vector(48 downto 0);
signal LogF_normal_pad :  std_logic_vector(48 downto 0);
signal lnaddX :  std_logic_vector(48 downto 0);
signal lnaddY :  std_logic_vector(48 downto 0);
signal Log_normal :  std_logic_vector(48 downto 0);
signal E_normal :  std_logic_vector(5 downto 0);
signal Log_normal_normd :  std_logic_vector(39 downto 0);
signal Z2o2_small_bs :  std_logic_vector(15 downto 0);
signal Z2o2_small_s :  std_logic_vector(30 downto 0);
signal Z2o2_small :  std_logic_vector(28 downto 0);
signal Z_small :  std_logic_vector(28 downto 0);
signal Log_smallY :  std_logic_vector(28 downto 0);
signal nsRCin :  std_logic;
signal Log_small, Log_small_d1 :  std_logic_vector(28 downto 0);
signal E0_sub, E0_sub_d1 :  std_logic_vector(1 downto 0);
signal ufl, ufl_d1, ufl_d2 :  std_logic;
signal E_small, E_small_d1 :  std_logic_vector(8 downto 0);
signal Log_small_normd, Log_small_normd_d1 :  std_logic_vector(26 downto 0);
signal E0offset :  std_logic_vector(8 downto 0);
signal ER :  std_logic_vector(8 downto 0);
signal Log_g :  std_logic_vector(26 downto 0);
-- signal round :  std_logic;
signal fraX :  std_logic_vector(31 downto 0);
signal fraY :  std_logic_vector(31 downto 0);
signal EFR :  std_logic_vector(31 downto 0);
constant g: positive := 4;
constant log2wF: positive := 5;
constant pfinal: positive := 13;
constant sfinal: positive := 27;
constant targetprec: positive := 40;
constant wE: positive := 9;
constant wF: positive := 23;
attribute rom_extract: string;
attribute rom_style: string;
attribute rom_extract of InvTable_0_9_10: component is "yes";
attribute rom_style of InvTable_0_9_10: component is "block";
begin
   process(clk)
      begin
         if clk'event and clk = '1' then
            XExnSgn_d1 <=  XExnSgn;
            XExnSgn_d2 <=  XExnSgn_d1;
            XExnSgn_d3 <=  XExnSgn_d2;
            XExnSgn_d4 <=  XExnSgn_d3;
            XExnSgn_d5 <=  XExnSgn_d4;
            XExnSgn_d6 <=  XExnSgn_d5;
            XExnSgn_d7 <=  XExnSgn_d6;
            XExnSgn_d8 <=  XExnSgn_d7;
            Y0_d1 <=  Y0;
            Y0_d2 <=  Y0_d1;
            sR_d1 <=  sR;
            sR_d2 <=  sR_d1;
            sR_d3 <=  sR_d2;
            sR_d4 <=  sR_d3;
            sR_d5 <=  sR_d4;
            sR_d6 <=  sR_d5;
            sR_d7 <=  sR_d6;
            sR_d77 <= sR_d6; --mod by JDH Sept 21, 2015
            sR_d8 <=  sR_d7;
            absZ0_d1 <=  absZ0;
            absE_d1 <=  absE;
            absE_d2 <=  absE_d1;
            absE_d3 <=  absE_d2;
            absE_d4 <=  absE_d3;
            absE_d5 <=  absE_d4;
            absE_d6 <=  absE_d5;
            EeqZero_d1 <=  EeqZero;
            lzo_d1 <=  lzo;
            lzo_d2 <=  lzo_d1;
            lzo_d3 <=  lzo_d2;
            lzo_d4 <=  lzo_d3;
            lzo_d5 <=  lzo_d4;
            lzo_d6 <=  lzo_d5;
            shiftvalinR_d1 <=  shiftvalinR;
            shiftvalinR_d2 <=  shiftvalinR_d1;
            shiftvalinR_d3 <=  shiftvalinR_d2;
            shiftvalinR_d4 <=  shiftvalinR_d3;
            shiftvalinR_d5 <=  shiftvalinR_d4;
            doRR_d1 <=  doRR;
            doRR_d2 <=  doRR_d1;
            doRR_d3 <=  doRR_d2;
            small_d1 <=  small;
            small_d2 <=  small_d1;
            small_d3 <=  small_d2;
            small_d4 <=  small_d3;
            small_d5 <=  small_d4;
            small_d6 <=  small_d5;
            small_d7 <=  small_d6;
            small_absZ0_normd_d1 <=  small_absZ0_normd;
            small_absZ0_normd_d2 <=  small_absZ0_normd_d1;
            small_absZ0_normd_d3 <=  small_absZ0_normd_d2;
            small_absZ0_normd_d4 <=  small_absZ0_normd_d3;
            small_absZ0_normd_d5 <=  small_absZ0_normd_d4;
            A0_d1 <=  A0;
            A0_d2 <=  A0_d1;
            A0_d3 <=  A0_d2;
            A0_d4 <=  A0_d3;
            A0_d5 <=  A0_d4;
            InvA0_d1 <=  InvA0;
            P0_d1 <=  P0;
            A1_d1 <=  A1;
            A1_d2 <=  A1_d1;
            ZM1_d1 <=  ZM1;
            EiYPB1_d1 <=  EiYPB1;
            Zfinal_d1 <=  Zfinal;
            Z2o2_full_dummy_d1 <=  Z2o2_full_dummy;
            Log1p_normal_d1 <=  Log1p_normal;
            S2_d1 <=  S2;
            Log_small_d1 <=  Log_small;
            E0_sub_d1 <=  E0_sub;
            ufl_d1 <=  ufl;
            ufl_d2 <=  ufl_d1;
            E_small_d1 <=  E_small;
            Log_small_normd_d1 <=  Log_small_normd;
         end if;
      end process;
   XExnSgn <=  X(wE+wF+2 downto wE+wF);
   FirstBit <=  X(wF-1);
   Y0 <= "1" & X(wF-1 downto 0) & "0" when FirstBit = '0' else "01" & X(wF-1 downto 0);
   Y0h <= Y0(wF downto 1);
   -- Sign of the result;
   sR <= '0'   when  (X(wE+wF-1 downto wF) = ('0' & (wE-2 downto 0 => '1')))  -- binade [1..2)
     else not X(wE+wF-1);                -- MSB of exponent
   absZ0 <=   Y0(wF-pfinal+1 downto 0)          when (sR='0') else
             ((wF-pfinal+1 downto 0 => '0') - Y0(wF-pfinal+1 downto 0));
   E <= (X(wE+wF-1 downto wF)) - ("0" & (wE-2 downto 1 => '1') & (not FirstBit));
   absE <= ((wE-1 downto 0 => '0') - E)   when sR = '1' else E;
   EeqZero <= '1' when E=(wE-1 downto 0 => '0') else '0';
   ---------------- cycle 0----------------
   lzoc1: LZOC_23_5_uid3  -- pipelineDepth=1 maxInDelay=5.69e-10
      port map ( clk  => clk,
                 rst  => rst,
                 I => Y0h,
                 O => lzo,
                 OZB => FirstBit);
   ---------------- cycle 1----------------
   pfinal_s <= "01101";
   shiftval <= ('0' & lzo) - ('0' & pfinal_s);
   shiftvalinL <= shiftval(3 downto 0);
   shiftvalinR <= shiftval(3 downto 0);
   doRR <= shiftval(log2wF); -- sign of the result
   small <= EeqZero_d1 and not(doRR);
   ---------------- cycle 1----------------
   -- The left shifter for the 'small' case
   small_lshift: LeftShifter_12_by_max_12_uid6  -- pipelineDepth=0 maxInDelay=2.85177e-09
      port map ( clk  => clk,
                 rst  => rst,
                 R => small_absZ0_normd_full,
                 S => shiftvalinL,
                 X => absZ0_d1);
   small_absZ0_normd <= small_absZ0_normd_full(11 downto 0); -- get rid of leading zeroes
   ----------------Synchro barrier, entering cycle 0----------------
   ---------------- The range reduction box ---------------
   A0 <= X(22 downto 14);
   ----------------Synchro barrier, entering cycle 1----------------
   -- First inv table
   itO: InvTable_0_9_10  -- pipelineDepth=0 maxInDelay=0
      port map ( clk  => clk,
                 rst  => rst,
                 X => A0_d1,
                 Y => InvA0);
   ----------------Synchro barrier, entering cycle 2----------------
   P0 <= InvA0_d1 * Y0_d2;

   ----------------Synchro barrier, entering cycle 3----------------
   Z1 <= P0_d1(25 downto 0);

   A1 <= Z1(25 downto 19);
   B1 <= Z1(18 downto 0);
   ZM1 <= Z1;
   ----------------Synchro barrier, entering cycle 4----------------
   P1 <= A1_d1*ZM1_d1;
   ----------------Synchro barrier, entering cycle 5----------------
    -- delay at multiplier output is 0
   ---------------- cycle 3----------------
   Y1 <= "1" & (6 downto 0 => '0') & Z1;
   EiY1 <= Y1(33 downto 7)  when A1(6) = '1'
     else  "0" & Y1(33 downto 8);
   addXIter1 <= "0" & B1 & (6 downto 0 => '0');
   addIter1_1: IntAdder_27_f200_uid11  -- pipelineDepth=0 maxInDelay=8.6e-11
      port map ( clk  => clk,
                 rst  => rst,
                 Cin =>  '0',
                 R => EiYPB1,
                 X => addXIter1,
                 Y => EiY1);

   ----------------Synchro barrier, entering cycle 4----------------
   Pp1 <= (0 downto 0 => '1') & not(P1(32 downto 7));
   addIter2_1: IntAdder_27_f200_uid18  -- pipelineDepth=0 maxInDelay=0
      port map ( clk  => clk,
                 rst  => rst,
                 Cin =>  '1',
                 R => Z2,
                 X => EiYPB1_d1,
                 Y => Pp1);

 -- the critical path at the adder output = 2.15172e-09
   Zfinal <= Z2;
   --  Synchro between RR box and case almost 1
   squarerIn <= Zfinal(sfinal-1 downto sfinal-16) when doRR_d3='1'
                    else (small_absZ0_normd_d3 & (3 downto 0 => '0'));
   squarer: IntSquarer_16_uid25  -- pipelineDepth=1 maxInDelay=3.11844e-09
      port map ( clk  => clk,
                 rst  => rst,
                 R => Z2o2_full,
                 X => squarerIn);
   ----------------Synchro barrier, entering cycle 5----------------
   Z2o2_full_dummy <= Z2o2_full;
   Z2o2_normal <= Z2o2_full_dummy (31  downto 19);
   addFinalLog1pY <= (pfinal downto 0  => '1') & not(Z2o2_normal);
   addFinalLog1p_normalAdder: IntAdder_27_f200_uid28  -- pipelineDepth=0 maxInDelay=8.8072e-10
      port map ( clk  => clk,
                 rst  => rst,
                 Cin =>  '1',
                 R => Log1p_normal,
                 X => Zfinal_d1,
                 Y => addFinalLog1pY);

   -- Now the log tables, as late as possible
   ----------------Synchro barrier, entering cycle 0----------------
   ----------------Synchro barrier, entering cycle 0----------------
   ----------------Synchro barrier, entering cycle 5----------------
   -- First log table
   ltO: LogTable_0_9_40  -- pipelineDepth=0 maxInDelay=0
      port map ( clk  => clk,
                 rst  => rst,
                 X => A0_d5,
                 Y => L0);
   S1 <= L0;
   lt1: LogTable_1_7_33  -- pipelineDepth=0 maxInDelay=0
      port map ( clk  => clk,
                 rst  => rst,
                 X => A1_d2,
                 Y => L1);
   sopX1 <= ((39 downto 33 => '0') & L1);
   adderS1: IntAdder_40_f200_uid45  -- pipelineDepth=0 maxInDelay=4.36e-10
      port map ( clk  => clk,
                 rst  => rst,
                 Cin =>  '0' ,
                 R => S2,
                 X => S1,
                 Y => sopX1);

   ----------------Synchro barrier, entering cycle 6----------------
   almostLog <= S2_d1;
   adderLogF_normalY <= ((targetprec-1 downto sfinal => '0') & Log1p_normal_d1);
   adderLogF_normal: IntAdder_40_f200_uid52  -- pipelineDepth=0 maxInDelay=0
      port map ( clk  => clk,
                 rst  => rst,
                 Cin => '0',
                 R => LogF_normal,
                 X => almostLog,
                 Y => adderLogF_normalY);
   ----------------Synchro barrier, entering cycle 6----------------
   Log2KCM: IntIntKCM_9_93032640_unsigned  -- pipelineDepth=0 maxInDelay=0
      port map ( clk  => clk,
                 rst  => rst,
                 R => absELog2,
                 X => absE_d6);
   ----------------Synchro barrier, entering cycle 6----------------
   absELog2_pad <=   absELog2 & (targetprec-wF-g-1 downto 0 => '0');
   LogF_normal_pad <= (wE-1  downto 0 => LogF_normal(targetprec-1))  & LogF_normal;
   lnaddX <= absELog2_pad;
   lnaddY <= LogF_normal_pad when sR_d6='0' else not(LogF_normal_pad);
   lnadder: IntAdder_49_f200_uid72  -- pipelineDepth=0 maxInDelay=2.58632e-09
      port map ( clk  => clk,
                 rst  => rst,
                 Cin => sR_d6,
                 R => Log_normal,
                 X => lnaddX,
                 Y => lnaddY);

   final_norm: LZCShifter_49_to_40_counting_64_uid79  -- pipelineDepth=2 maxInDelay=4.82604e-09
      port map ( clk  => clk,
                 rst  => rst,
                 Count => E_normal,
                 I => Log_normal,
                 O => Log_normal_normd);
   Z2o2_small_bs <= Z2o2_full_dummy_d1(31 downto 16);
   ao_rshift: RightShifter_16_by_max_15_uid82  -- pipelineDepth=0 maxInDelay=2.77888e-09
      port map ( clk  => clk,
                 rst  => rst,
                 R => Z2o2_small_s,
                 S => shiftvalinR_d5,
                 X => Z2o2_small_bs);
   ---------------- cycle 6----------------
   -- output delay at shifter output is 1.33176e-09
     -- send the MSB to position pfinal
   Z2o2_small <=  (pfinal-1 downto 0  => '0') & Z2o2_small_s(30 downto 15);
   -- mantissa will be either Y0-z^2/2  or  -Y0+z^2/2,  depending on sR
   Z_small <= small_absZ0_normd_d5 & (16 downto 0 => '0');
   Log_smallY <= Z2o2_small when sR_d6='1' else not(Z2o2_small);
   nsRCin <= not ( sR_d6 );
   log_small_adder: IntAdder_29_f200_uid85  -- pipelineDepth=0 maxInDelay=2.3072e-09
      port map ( clk  => clk,
                 rst  => rst,
                 Cin => nsRCin,
                 R => Log_small,
                 X => Z_small,
                 Y => Log_smallY);

 -- critical path here is 3.6422e-09
   -- Possibly subtract 1 or 2 to the exponent, depending on the LZC of Log_small
   E0_sub <=   "11" when Log_small(wF+g+1) = '1'
          else "10" when Log_small(wF+g+1 downto wF+g) = "01"
          else "01" ;
   -- The smallest log will be log(1+2^{-wF}) \approx 2^{-wF}  = 2^-23
   -- The smallest representable number is 2^{1-2^(wE-1)} = 2^-255
   -- No underflow possible
   ufl <= '0';
   ----------------Synchro barrier, entering cycle 7----------------
   E_small <=  ("0" & (wE-2 downto 2 => '1') & E0_sub_d1)  -  ((wE-1 downto 5 => '0') & lzo_d6) ;
   Log_small_normd <= Log_small_d1(wF+g+1 downto 2) when Log_small_d1(wF+g+1)='1'
           else Log_small_d1(wF+g downto 1)  when Log_small_d1(wF+g)='1'  -- remove the first zero
           else Log_small_d1(wF+g-1 downto 0)  ; -- remove two zeroes (extremely rare, 001000000 only)
   ----------------Synchro barrier, entering cycle 8----------------
   E0offset <= "100000111"; -- E0 + wE
   ER <= E_small_d1(8 downto 0) when small_d7='1'
      else E0offset - ((8 downto 6 => '0') & E_normal);
   ---------------- cycle 8----------------
   Log_g <=  Log_small_normd_d1(wF+g-2 downto 0) & "0" when small_d7='1'           -- remove implicit 1
      else Log_normal_normd(targetprec-2 downto targetprec-wF-g-1 );  -- remove implicit 1
   round <= Log_g(g-1) ; -- sticky is always 1 for a transcendental function
   -- if round leads to a change of binade, the carry propagation magically updates both mantissa and exponent
   fraX <= (ER & Log_g(wF+g-1 downto g)) ;
--   fraY <= ((wE+wF-1 downto 1 => '0') & round);
   fraY <= ((wE+wF-1 downto 1 => '0') & roundit); -- mod by JDH Sept 21, 2015
   finalRoundAdder: IntAdder_32_f200_uid92  -- pipelineDepth=0 maxInDelay=2.86488e-09
      port map ( clk  => clk,
                 rst  => rst,
                 Cin => '0',
                 R => EFR,
                 X => fraX,
                 Y => fraY);
   R(wE+wF+2 downto wE+wF) <= "110" when ((XExnSgn_d8(2) and (XExnSgn_d8(1) or XExnSgn_d8(0))) or (XExnSgn_d8(1) and XExnSgn_d8(0))) = '1' else
                              "101" when XExnSgn_d8(2 downto 1) = "00"  else
                              "100" when XExnSgn_d8(2 downto 1) = "10"  else
                              "00" & sR_d8 when (((Log_normal_normd(targetprec-1)='0') and (small_d7='0')) or ( (Log_small_normd_d1 (wF+g-1)='0') and (small_d7='1'))) or (ufl_d2 = '1') else
                               "01" & sR_d8;
   R(wE+wF-1 downto 0) <=  EFR;
end architecture;
