kuanwoo/SYMPL64_FloatingPoint_RISC-/FloPoCo_operators/Mul_Clk9.vhdl

-- vagrant@vagrant-ubuntu-trusty-32:~/flopoco-3.0.beta5$ ./flopoco -name=Mul_Clk -frequency=200 -useHardMult=no FPMult 9 23 23
-- Updating entity name to: Mul_Clk
-- 
-- Final report:
-- Entity SmallMultTableP3x3r6XuYu_g
--    Not pipelined
-- Entity Compressor_6_3_h
--    Not pipelined
-- Entity Compressor_14_3_i
--    Not pipelined
-- Entity Compressor_4_3_j
--    Not pipelined
-- Entity Compressor_23_3_k
--    Not pipelined
-- Entity Compressor_13_3_L
--    Not pipelined
-- Entity Compressor_3_2_m
--    Not pipelined
-- |   |---Entity IntAdder_48_f200_uid101
-- |   |      Not pipelined
-- |---Entity IntMultiplier_UsingDSP_24_24_48_unsigned_uid4
-- |      Pipeline depth = 1
-- |---Entity IntAdder_34_f200_uid109
-- |      Not pipelined
-- Entity Mul_Clk
--    Pipeline depth = 1
-- Output file: flopoco.vhdl
--------------------------------------------------------------------------------
--                          SmallMultTableP3x3r6XuYu_g
-- This operator is part of the Infinite Virtual Library FloPoCoLib
-- All rights reserved
-- Authors: Florent de Dinechin (2007-2012)
--------------------------------------------------------------------------------
library ieee;
use ieee.std_logic_1164.all;
use ieee.numeric_std.all;
library work;
entity SmallMultTableP3x3r6XuYu_g is
   port ( clk, rst : in std_logic;
          X : in  std_logic_vector(5 downto 0);
          Y : out  std_logic_vector(5 downto 0)   );
end entity;

architecture arch of SmallMultTableP3x3r6XuYu_g is
begin
  with X select  Y <=
   "000000" when "000000",
   "000000" when "000001",
   "000000" when "000010",
   "000000" when "000011",
   "000000" when "000100",
   "000000" when "000101",
   "000000" when "000110",
   "000000" when "000111",
   "000000" when "001000",
   "000001" when "001001",
   "000010" when "001010",
   "000011" when "001011",
   "000100" when "001100",
   "000101" when "001101",
   "000110" when "001110",
   "000111" when "001111",
   "000000" when "010000",
   "000010" when "010001",
   "000100" when "010010",
   "000110" when "010011",
   "001000" when "010100",
   "001010" when "010101",
   "001100" when "010110",
   "001110" when "010111",
   "000000" when "011000",
   "000011" when "011001",
   "000110" when "011010",
   "001001" when "011011",
   "001100" when "011100",
   "001111" when "011101",
   "010010" when "011110",
   "010101" when "011111",
   "000000" when "100000",
   "000100" when "100001",
   "001000" when "100010",
   "001100" when "100011",
   "010000" when "100100",
   "010100" when "100101",
   "011000" when "100110",
   "011100" when "100111",
   "000000" when "101000",
   "000101" when "101001",
   "001010" when "101010",
   "001111" when "101011",
   "010100" when "101100",
   "011001" when "101101",
   "011110" when "101110",
   "100011" when "101111",
   "000000" when "110000",
   "000110" when "110001",
   "001100" when "110010",
   "010010" when "110011",
   "011000" when "110100",
   "011110" when "110101",
   "100100" when "110110",
   "101010" when "110111",
   "000000" when "111000",
   "000111" when "111001",
   "001110" when "111010",
   "010101" when "111011",
   "011100" when "111100",
   "100011" when "111101",
   "101010" when "111110",
   "110001" when "111111",
   "------" when others;
end architecture;

--------------------------------------------------------------------------------
--                               Compressor_6_3_h
-- This operator is part of the Infinite Virtual Library FloPoCoLib
-- All rights reserved
-- Authors: Bogdan Popa, Illyes Kinga, 2012
--------------------------------------------------------------------------------
-- combinatorial

library ieee;
use ieee.std_logic_1164.all;
use ieee.std_logic_arith.all;
use ieee.std_logic_unsigned.all;
library std;
use std.textio.all;
library work;

entity Compressor_6_3_h is
   port ( X0 : in  std_logic_vector(5 downto 0);
          R : out  std_logic_vector(2 downto 0)   );
end entity;

architecture arch of Compressor_6_3_h is
signal X :  std_logic_vector(5 downto 0);
begin
   X <=X0 ;
   with X select R <=
      "000" when "000000",
      "001" when "000001",
      "001" when "000010",
      "010" when "000011",
      "001" when "000100",
      "010" when "000101",
      "010" when "000110",
      "011" when "000111",
      "001" when "001000",
      "010" when "001001",
      "010" when "001010",
      "011" when "001011",
      "010" when "001100",
      "011" when "001101",
      "011" when "001110",
      "100" when "001111",
      "001" when "010000",
      "010" when "010001",
      "010" when "010010",
      "011" when "010011",
      "010" when "010100",
      "011" when "010101",
      "011" when "010110",
      "100" when "010111",
      "010" when "011000",
      "011" when "011001",
      "011" when "011010",
      "100" when "011011",
      "011" when "011100",
      "100" when "011101",
      "100" when "011110",
      "101" when "011111",
      "001" when "100000",
      "010" when "100001",
      "010" when "100010",
      "011" when "100011",
      "010" when "100100",
      "011" when "100101",
      "011" when "100110",
      "100" when "100111",
      "010" when "101000",
      "011" when "101001",
      "011" when "101010",
      "100" when "101011",
      "011" when "101100",
      "100" when "101101",
      "100" when "101110",
      "101" when "101111",
      "010" when "110000",
      "011" when "110001",
      "011" when "110010",
      "100" when "110011",
      "011" when "110100",
      "100" when "110101",
      "100" when "110110",
      "101" when "110111",
      "011" when "111000",
      "100" when "111001",
      "100" when "111010",
      "101" when "111011",
      "100" when "111100",
      "101" when "111101",
      "101" when "111110",
      "110" when "111111",
      "---" when others;

end architecture;

--------------------------------------------------------------------------------
--                              Compressor_14_3_i
-- This operator is part of the Infinite Virtual Library FloPoCoLib
-- All rights reserved
-- Authors: Bogdan Popa, Illyes Kinga, 2012
--------------------------------------------------------------------------------
-- combinatorial

library ieee;
use ieee.std_logic_1164.all;
use ieee.std_logic_arith.all;
use ieee.std_logic_unsigned.all;
library std;
use std.textio.all;
library work;

entity Compressor_14_3_i is
   port ( X0 : in  std_logic_vector(3 downto 0);
          X1 : in  std_logic_vector(0 downto 0);
          R : out  std_logic_vector(2 downto 0)   );
end entity;

architecture arch of Compressor_14_3_i is
signal X :  std_logic_vector(4 downto 0);
begin
   X <=X1 & X0 ;
   with X select R <=
      "000" when "00000",
      "001" when "00001",
      "001" when "00010",
      "010" when "00011",
      "001" when "00100",
      "010" when "00101",
      "010" when "00110",
      "011" when "00111",
      "001" when "01000",
      "010" when "01001",
      "010" when "01010",
      "011" when "01011",
      "010" when "01100",
      "011" when "01101",
      "011" when "01110",
      "100" when "01111",
      "010" when "10000",
      "011" when "10001",
      "011" when "10010",
      "100" when "10011",
      "011" when "10100",
      "100" when "10101",
      "100" when "10110",
      "101" when "10111",
      "011" when "11000",
      "100" when "11001",
      "100" when "11010",
      "101" when "11011",
      "100" when "11100",
      "101" when "11101",
      "101" when "11110",
      "110" when "11111",
      "---" when others;

end architecture;

--------------------------------------------------------------------------------
--                               Compressor_4_3_j
-- This operator is part of the Infinite Virtual Library FloPoCoLib
-- All rights reserved
-- Authors: Bogdan Popa, Illyes Kinga, 2012
--------------------------------------------------------------------------------
-- combinatorial

library ieee;
use ieee.std_logic_1164.all;
use ieee.std_logic_arith.all;
use ieee.std_logic_unsigned.all;
library std;
use std.textio.all;
library work;

entity Compressor_4_3_j is
   port ( X0 : in  std_logic_vector(3 downto 0);
          R : out  std_logic_vector(2 downto 0)   );
end entity;

architecture arch of Compressor_4_3_j is
signal X :  std_logic_vector(3 downto 0);
begin
   X <=X0 ;
   with X select R <=
      "000" when "0000",
      "001" when "0001",
      "001" when "0010",
      "010" when "0011",
      "001" when "0100",
      "010" when "0101",
      "010" when "0110",
      "011" when "0111",
      "001" when "1000",
      "010" when "1001",
      "010" when "1010",
      "011" when "1011",
      "010" when "1100",
      "011" when "1101",
      "011" when "1110",
      "100" when "1111",
      "---" when others;

end architecture;

--------------------------------------------------------------------------------
--                              Compressor_23_3_k
-- This operator is part of the Infinite Virtual Library FloPoCoLib
-- All rights reserved
-- Authors: Bogdan Popa, Illyes Kinga, 2012
--------------------------------------------------------------------------------
-- combinatorial

library ieee;
use ieee.std_logic_1164.all;
use ieee.std_logic_arith.all;
use ieee.std_logic_unsigned.all;
library std;
use std.textio.all;
library work;

entity Compressor_23_3_k is
   port ( X0 : in  std_logic_vector(2 downto 0);
          X1 : in  std_logic_vector(1 downto 0);
          R : out  std_logic_vector(2 downto 0)   );
end entity;

architecture arch of Compressor_23_3_k is
signal X :  std_logic_vector(4 downto 0);
begin
   X <=X1 & X0 ;
   with X select R <=
      "000" when "00000",
      "001" when "00001",
      "001" when "00010",
      "010" when "00011",
      "001" when "00100",
      "010" when "00101",
      "010" when "00110",
      "011" when "00111",
      "010" when "01000",
      "011" when "01001",
      "011" when "01010",
      "100" when "01011",
      "011" when "01100",
      "100" when "01101",
      "100" when "01110",
      "101" when "01111",
      "010" when "10000",
      "011" when "10001",
      "011" when "10010",
      "100" when "10011",
      "011" when "10100",
      "100" when "10101",
      "100" when "10110",
      "101" when "10111",
      "100" when "11000",
      "101" when "11001",
      "101" when "11010",
      "110" when "11011",
      "101" when "11100",
      "110" when "11101",
      "110" when "11110",
      "111" when "11111",
      "---" when others;

end architecture;

--------------------------------------------------------------------------------
--                              Compressor_13_3_L
-- This operator is part of the Infinite Virtual Library FloPoCoLib
-- All rights reserved
-- Authors: Bogdan Popa, Illyes Kinga, 2012
--------------------------------------------------------------------------------
-- combinatorial

library ieee;
use ieee.std_logic_1164.all;
use ieee.std_logic_arith.all;
use ieee.std_logic_unsigned.all;
library std;
use std.textio.all;
library work;

entity Compressor_13_3_L is
   port ( X0 : in  std_logic_vector(2 downto 0);
          X1 : in  std_logic_vector(0 downto 0);
          R : out  std_logic_vector(2 downto 0)   );
end entity;

architecture arch of Compressor_13_3_L is
signal X :  std_logic_vector(3 downto 0);
begin
   X <=X1 & X0 ;
   with X select R <=
      "000" when "0000",
      "001" when "0001",
      "001" when "0010",
      "010" when "0011",
      "001" when "0100",
      "010" when "0101",
      "010" when "0110",
      "011" when "0111",
      "010" when "1000",
      "011" when "1001",
      "011" when "1010",
      "100" when "1011",
      "011" when "1100",
      "100" when "1101",
      "100" when "1110",
      "101" when "1111",
      "---" when others;

end architecture;

--------------------------------------------------------------------------------
--                               Compressor_3_2_m
-- This operator is part of the Infinite Virtual Library FloPoCoLib
-- All rights reserved
-- Authors: Bogdan Popa, Illyes Kinga, 2012
--------------------------------------------------------------------------------
-- combinatorial

library ieee;
use ieee.std_logic_1164.all;
use ieee.std_logic_arith.all;
use ieee.std_logic_unsigned.all;
library std;
use std.textio.all;
library work;

entity Compressor_3_2_m is
   port ( X0 : in  std_logic_vector(2 downto 0);
          R : out  std_logic_vector(1 downto 0)   );
end entity;

architecture arch of Compressor_3_2_m is
signal X :  std_logic_vector(2 downto 0);
begin
   X <=X0 ;
   with X select R <=
      "00" when "000",
      "01" when "001",
      "01" when "010",
      "10" when "011",
      "01" when "100",
      "10" when "101",
      "10" when "110",
      "11" when "111",
      "--" when others;

end architecture;

--------------------------------------------------------------------------------
--                          IntAdder_48_f200_uid101
--                    (IntAdderAlternative_48_f200_uid105)
-- This operator is part of the Infinite Virtual Library FloPoCoLib
-- All rights reserved
-- Authors: Bogdan Pasca, Florent de Dinechin (2008-2010)
--------------------------------------------------------------------------------
-- Pipeline depth: 0 cycles

library ieee;
use ieee.std_logic_1164.all;
use ieee.std_logic_arith.all;
use ieee.std_logic_unsigned.all;
library std;
use std.textio.all;
library work;

entity IntAdder_48_f200_uid101 is
   port ( clk, rst : in std_logic;
          X : in  std_logic_vector(47 downto 0);
          Y : in  std_logic_vector(47 downto 0);
          Cin : in  std_logic;
          R : out  std_logic_vector(47 downto 0)   );
end entity;

architecture arch of IntAdder_48_f200_uid101 is
begin
   process(clk)
      begin
         if clk'event and clk = '1' then
         end if;
      end process;
   --Alternative
    R <= X + Y + Cin;
end architecture;

--------------------------------------------------------------------------------
--               IntMultiplier_UsingDSP_24_24_48_unsigned_uid4
-- This operator is part of the Infinite Virtual Library FloPoCoLib
-- All rights reserved
-- Authors: Florent de Dinechin, Kinga Illyes, Bogdan Popa, Bogdan Pasca, 2012
--------------------------------------------------------------------------------
-- Pipeline depth: 1 cycles

library ieee;
use ieee.std_logic_1164.all;
use ieee.numeric_std.all;
library std;
use std.textio.all;
library work;

entity IntMultiplier_UsingDSP_24_24_48_unsigned_uid4 is
   port ( clk, rst : in std_logic;
          X : in  std_logic_vector(23 downto 0);
          Y : in  std_logic_vector(23 downto 0);
          R : out  std_logic_vector(47 downto 0)   );
end entity;

architecture arch of IntMultiplier_UsingDSP_24_24_48_unsigned_uid4 is
   component Compressor_13_3_L is
      port ( X0 : in  std_logic_vector(2 downto 0);
             X1 : in  std_logic_vector(0 downto 0);
             R : out  std_logic_vector(2 downto 0)   );
   end component;

   component Compressor_14_3_i is
      port ( X0 : in  std_logic_vector(3 downto 0);
             X1 : in  std_logic_vector(0 downto 0);
             R : out  std_logic_vector(2 downto 0)   );
   end component;

   component Compressor_23_3_k is
      port ( X0 : in  std_logic_vector(2 downto 0);
             X1 : in  std_logic_vector(1 downto 0);
             R : out  std_logic_vector(2 downto 0)   );
   end component;

   component Compressor_3_2_m is
      port ( X0 : in  std_logic_vector(2 downto 0);
             R : out  std_logic_vector(1 downto 0)   );
   end component;

   component Compressor_4_3_j is
      port ( X0 : in  std_logic_vector(3 downto 0);
             R : out  std_logic_vector(2 downto 0)   );
   end component;

   component Compressor_6_3_h is
      port ( X0 : in  std_logic_vector(5 downto 0);
             R : out  std_logic_vector(2 downto 0)   );
   end component;

   component IntAdder_48_f200_uid101 is
      port ( clk, rst : in std_logic;
             X : in  std_logic_vector(47 downto 0);
             Y : in  std_logic_vector(47 downto 0);
             Cin : in  std_logic;
             R : out  std_logic_vector(47 downto 0)   );
   end component;

   component SmallMultTableP3x3r6XuYu_g is
      port ( clk, rst : in std_logic;
             X : in  std_logic_vector(5 downto 0);
             Y : out  std_logic_vector(5 downto 0)   );
   end component;

signal XX_m5 :  std_logic_vector(23 downto 0);
signal YY_m5 :  std_logic_vector(23 downto 0);
signal Xp_m5b7 :  std_logic_vector(23 downto 0);
signal Yp_m5b7 :  std_logic_vector(8 downto 0);
signal x_m5b7_0 :  std_logic_vector(2 downto 0);
signal x_m5b7_1 :  std_logic_vector(2 downto 0);
signal x_m5b7_2 :  std_logic_vector(2 downto 0);
signal x_m5b7_3 :  std_logic_vector(2 downto 0);
signal x_m5b7_4 :  std_logic_vector(2 downto 0);
signal x_m5b7_5 :  std_logic_vector(2 downto 0);
signal x_m5b7_6 :  std_logic_vector(2 downto 0);
signal x_m5b7_7 :  std_logic_vector(2 downto 0);
signal y_m5b7_0 :  std_logic_vector(2 downto 0);
signal y_m5b7_1 :  std_logic_vector(2 downto 0);
signal y_m5b7_2 :  std_logic_vector(2 downto 0);
signal Y0X0_7_m5 :  std_logic_vector(5 downto 0);
signal PP7X0Y0_m5 :  std_logic_vector(5 downto 0);
signal heap_bh6_w0_0 :  std_logic;
signal heap_bh6_w1_0, heap_bh6_w1_0_d1 :  std_logic;
signal heap_bh6_w2_0, heap_bh6_w2_0_d1 :  std_logic;
signal heap_bh6_w3_0 :  std_logic;
signal Y0X1_7_m5 :  std_logic_vector(5 downto 0);
signal PP7X1Y0_m5 :  std_logic_vector(5 downto 0);
signal heap_bh6_w3_1 :  std_logic;
signal heap_bh6_w4_0 :  std_logic;
signal heap_bh6_w5_0 :  std_logic;
signal heap_bh6_w6_0 :  std_logic;
signal Y0X2_7_m5 :  std_logic_vector(5 downto 0);
signal PP7X2Y0_m5 :  std_logic_vector(5 downto 0);
signal heap_bh6_w6_1 :  std_logic;
signal heap_bh6_w7_0 :  std_logic;
signal heap_bh6_w8_0 :  std_logic;
signal heap_bh6_w9_0 :  std_logic;
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
            heap_bh6_w8_11_d1 <=  heap_bh6_w8_11;
            heap_bh6_w9_11_d1 <=  heap_bh6_w9_11;
            heap_bh6_w9_12_d1 <=  heap_bh6_w9_12;
            heap_bh6_w10_11_d1 <=  heap_bh6_w10_11;
            heap_bh6_w30_2_d1 <=  heap_bh6_w30_2;
            heap_bh6_w31_1_d1 <=  heap_bh6_w31_1;
            heap_bh6_w11_12_d1 <=  heap_bh6_w11_12;
            heap_bh6_w12_13_d1 <=  heap_bh6_w12_13;
            heap_bh6_w13_13_d1 <=  heap_bh6_w13_13;
            heap_bh6_w26_8_d1 <=  heap_bh6_w26_8;
            heap_bh6_w27_8_d1 <=  heap_bh6_w27_8;
            heap_bh6_w15_14_d1 <=  heap_bh6_w15_14;
            heap_bh6_w16_13_d1 <=  heap_bh6_w16_13;
            heap_bh6_w19_13_d1 <=  heap_bh6_w19_13;
            heap_bh6_w22_13_d1 <=  heap_bh6_w22_13;
            heap_bh6_w25_10_d1 <=  heap_bh6_w25_10;
            heap_bh6_w26_9_d1 <=  heap_bh6_w26_9;
            heap_bh6_w17_13_d1 <=  heap_bh6_w17_13;
            heap_bh6_w18_15_d1 <=  heap_bh6_w18_15;
            heap_bh6_w19_14_d1 <=  heap_bh6_w19_14;
            heap_bh6_w20_13_d1 <=  heap_bh6_w20_13;
            heap_bh6_w21_15_d1 <=  heap_bh6_w21_15;
            heap_bh6_w22_14_d1 <=  heap_bh6_w22_14;
            heap_bh6_w23_13_d1 <=  heap_bh6_w23_13;
            heap_bh6_w24_14_d1 <=  heap_bh6_w24_14;
            heap_bh6_w25_11_d1 <=  heap_bh6_w25_11;
            heap_bh6_w28_5_d1 <=  heap_bh6_w28_5;
            heap_bh6_w29_4_d1 <=  heap_bh6_w29_4;
            heap_bh6_w30_3_d1 <=  heap_bh6_w30_3;
         end if;
      end process;
   XX_m5 <= X ;
   YY_m5 <= Y ;
   -- code generated by IntMultiplier::buildHeapLogicOnly()
   -- buildheaplogiconly called for lsbX=0 lsbY=0 msbX=24 msbY=7
   Xp_m5b7 <= XX_m5(23 downto 0) & "";
   Yp_m5b7 <= YY_m5(6 downto 0) & "00";
   x_m5b7_0 <= Xp_m5b7(2 downto 0);
   x_m5b7_1 <= Xp_m5b7(5 downto 3);
   x_m5b7_2 <= Xp_m5b7(8 downto 6);
   x_m5b7_3 <= Xp_m5b7(11 downto 9);
   x_m5b7_4 <= Xp_m5b7(14 downto 12);
   x_m5b7_5 <= Xp_m5b7(17 downto 15);
   x_m5b7_6 <= Xp_m5b7(20 downto 18);
   x_m5b7_7 <= Xp_m5b7(23 downto 21);
   y_m5b7_0 <= Yp_m5b7(2 downto 0);
   y_m5b7_1 <= Yp_m5b7(5 downto 3);
   y_m5b7_2 <= Yp_m5b7(8 downto 6);
   ----------------Synchro barrier, entering cycle 0----------------
   -- Partial product row number 0
   Y0X0_7_m5 <= y_m5b7_0 & x_m5b7_0;
   PP_m5_7X0Y0_Tbl: SmallMultTableP3x3r6XuYu_g  -- pipelineDepth=0 maxInDelay=0
      port map ( clk  => clk,
                 rst  => rst,
                 X => Y0X0_7_m5,
                 Y => PP7X0Y0_m5);
   -- Adding the relevant bits to the heap of bits
   heap_bh6_w0_0 <= PP7X0Y0_m5(2); -- cycle= 0 cp= 5.9176e-10
   heap_bh6_w1_0 <= PP7X0Y0_m5(3); -- cycle= 0 cp= 5.9176e-10
   heap_bh6_w2_0 <= PP7X0Y0_m5(4); -- cycle= 0 cp= 5.9176e-10
   heap_bh6_w3_0 <= PP7X0Y0_m5(5); -- cycle= 0 cp= 5.9176e-10

   Y0X1_7_m5 <= y_m5b7_0 & x_m5b7_1;
   PP_m5_7X1Y0_Tbl: SmallMultTableP3x3r6XuYu_g  -- pipelineDepth=0 maxInDelay=0
      port map ( clk  => clk,
                 rst  => rst,
                 X => Y0X1_7_m5,
                 Y => PP7X1Y0_m5);
   -- Adding the relevant bits to the heap of bits
   heap_bh6_w3_1 <= PP7X1Y0_m5(2); -- cycle= 0 cp= 5.9176e-10
   heap_bh6_w4_0 <= PP7X1Y0_m5(3); -- cycle= 0 cp= 5.9176e-10
   heap_bh6_w5_0 <= PP7X1Y0_m5(4); -- cycle= 0 cp= 5.9176e-10
   heap_bh6_w6_0 <= PP7X1Y0_m5(5); -- cycle= 0 cp= 5.9176e-10

   Y0X2_7_m5 <= y_m5b7_0 & x_m5b7_2;
   PP_m5_7X2Y0_Tbl: SmallMultTableP3x3r6XuYu_g  -- pipelineDepth=0 maxInDelay=0
      port map ( clk  => clk,
                 rst  => rst,
                 X => Y0X2_7_m5,
                 Y => PP7X2Y0_m5);
   -- Adding the relevant bits to the heap of bits
   heap_bh6_w6_1 <= PP7X2Y0_m5(2); -- cycle= 0 cp= 5.9176e-10
   heap_bh6_w7_0 <= PP7X2Y0_m5(3); -- cycle= 0 cp= 5.9176e-10
   heap_bh6_w8_0 <= PP7X2Y0_m5(4); -- cycle= 0 cp= 5.9176e-10
   heap_bh6_w9_0 <= PP7X2Y0_m5(5); -- cycle= 0 cp= 5.9176e-10

   Y0X3_7_m5 <= y_m5b7_0 & x_m5b7_3;
   PP_m5_7X3Y0_Tbl: SmallMultTableP3x3r6XuYu_g  -- pipelineDepth=0 maxInDelay=0
      port map ( clk  => clk,
                 rst  => rst,
                 X => Y0X3_7_m5,
                 Y => PP7X3Y0_m5);
   -- Adding the relevant bits to the heap of bits
   heap_bh6_w9_1 <= PP7X3Y0_m5(2); -- cycle= 0 cp= 5.9176e-10
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
                 X1 => CompressorIn_bh6_55_95);
   heap_bh6_w24_13 <= CompressorOut_bh6_55_55(0); -- cycle= 0 cp= 3.44844e-09
   heap_bh6_w25_10 <= CompressorOut_bh6_55_55(1); -- cycle= 0 cp= 3.44844e-09
   heap_bh6_w26_9 <= CompressorOut_bh6_55_55(2); -- cycle= 0 cp= 3.44844e-09

   ----------------Synchro barrier, entering cycle 0----------------
   CompressorIn_bh6_56_96 <= heap_bh6_w17_5 & heap_bh6_w17_11 & heap_bh6_w17_12;
   CompressorIn_bh6_56_97(0) <= heap_bh6_w18_14;
   Compressor_bh6_56: Compressor_13_3_L
      port map ( R => CompressorOut_bh6_56_56   ,
                 X0 => CompressorIn_bh6_56_96,
                 X1 => CompressorIn_bh6_56_97);
   heap_bh6_w17_13 <= CompressorOut_bh6_56_56(0); -- cycle= 0 cp= 3.97916e-09
   heap_bh6_w18_15 <= CompressorOut_bh6_56_56(1); -- cycle= 0 cp= 3.97916e-09
   heap_bh6_w19_14 <= CompressorOut_bh6_56_56(2); -- cycle= 0 cp= 3.97916e-09

   ----------------Synchro barrier, entering cycle 0----------------
   CompressorIn_bh6_57_98 <= heap_bh6_w20_5 & heap_bh6_w20_11 & heap_bh6_w20_12;
   CompressorIn_bh6_57_99(0) <= heap_bh6_w21_14;
   Compressor_bh6_57: Compressor_13_3_L
      port map ( R => CompressorOut_bh6_57_57   ,
                 X0 => CompressorIn_bh6_57_98,
                 X1 => CompressorIn_bh6_57_99);
   heap_bh6_w20_13 <= CompressorOut_bh6_57_57(0); -- cycle= 0 cp= 3.97916e-09
   heap_bh6_w21_15 <= CompressorOut_bh6_57_57(1); -- cycle= 0 cp= 3.97916e-09
   heap_bh6_w22_14 <= CompressorOut_bh6_57_57(2); -- cycle= 0 cp= 3.97916e-09

   ----------------Synchro barrier, entering cycle 0----------------
   CompressorIn_bh6_58_100 <= heap_bh6_w23_5 & heap_bh6_w23_11 & heap_bh6_w23_12;
   CompressorIn_bh6_58_101(0) <= heap_bh6_w24_13;
   Compressor_bh6_58: Compressor_13_3_L
      port map ( R => CompressorOut_bh6_58_58   ,
                 X0 => CompressorIn_bh6_58_100,
                 X1 => CompressorIn_bh6_58_101);
   heap_bh6_w23_13 <= CompressorOut_bh6_58_58(0); -- cycle= 0 cp= 3.97916e-09
   heap_bh6_w24_14 <= CompressorOut_bh6_58_58(1); -- cycle= 0 cp= 3.97916e-09
   heap_bh6_w25_11 <= CompressorOut_bh6_58_58(2); -- cycle= 0 cp= 3.97916e-09

   ----------------Synchro barrier, entering cycle 0----------------
   CompressorIn_bh6_59_102 <= heap_bh6_w28_3 & heap_bh6_w28_1 & heap_bh6_w28_4;
   CompressorIn_bh6_59_103(0) <= heap_bh6_w29_3;
   Compressor_bh6_59: Compressor_13_3_L
      port map ( R => CompressorOut_bh6_59_59   ,
                 X0 => CompressorIn_bh6_59_102,
                 X1 => CompressorIn_bh6_59_103);
   heap_bh6_w28_5 <= CompressorOut_bh6_59_59(0); -- cycle= 0 cp= 3.97916e-09
   heap_bh6_w29_4 <= CompressorOut_bh6_59_59(1); -- cycle= 0 cp= 3.97916e-09
   heap_bh6_w30_3 <= CompressorOut_bh6_59_59(2); -- cycle= 0 cp= 3.97916e-09
   ----------------Synchro barrier, entering cycle 0----------------
   ----------------Synchro barrier, entering cycle 1----------------
   finalAdderIn0_bh6 <= "0" & heap_bh6_w47_0_d1 & heap_bh6_w46_0_d1 & heap_bh6_w45_0_d1 & heap_bh6_w44_0_d1 & heap_bh6_w43_0_d1 & heap_bh6_w42_0_d1 & heap_bh6_w41_0_d1 & heap_bh6_w40_0_d1 & heap_bh6_w39_0_d1 & heap_bh6_w38_0_d1 & heap_bh6_w37_0_d1 & heap_bh6_w36_0_d1 & heap_bh6_w35_0_d1 & heap_bh6_w34_0_d1 & heap_bh6_w33_0_d1 & heap_bh6_w32_0_d1 & heap_bh6_w31_0_d1 & heap_bh6_w30_2_d1 & heap_bh6_w29_4_d1 & heap_bh6_w28_5_d1 & heap_bh6_w27_7_d1 & heap_bh6_w26_9_d1 & heap_bh6_w25_10_d1 & heap_bh6_w24_14_d1 & heap_bh6_w23_13_d1 & heap_bh6_w22_13_d1 & heap_bh6_w21_15_d1 & heap_bh6_w20_13_d1 & heap_bh6_w19_13_d1 & heap_bh6_w18_15_d1 & heap_bh6_w17_13_d1 & heap_bh6_w16_13_d1 & heap_bh6_w15_14_d1 & heap_bh6_w14_5_d1 & heap_bh6_w13_12_d1 & heap_bh6_w12_13_d1 & heap_bh6_w11_12_d1 & heap_bh6_w10_5_d1 & heap_bh6_w9_12_d1 & heap_bh6_w8_5_d1 & heap_bh6_w7_10_d1 & heap_bh6_w6_8_d1 & heap_bh6_w5_5_d1 & heap_bh6_w4_5_d1 & heap_bh6_w3_3_d1 & heap_bh6_w2_1_d1 & heap_bh6_w1_1_d1;
   finalAdderIn1_bh6 <= "0" & '0' & '0' & '0' & '0' & '0' & '0' & '0' & '0' & '0' & '0' & '0' & '0' & '0' & '0' & '0' & '0' & heap_bh6_w31_1_d1 & heap_bh6_w30_3_d1 & '0' & '0' & heap_bh6_w27_8_d1 & heap_bh6_w26_8_d1 & heap_bh6_w25_11_d1 & '0' & '0' & heap_bh6_w22_14_d1 & '0' & '0' & heap_bh6_w19_14_d1 & '0' & '0' & '0' & '0' & heap_bh6_w14_11_d1 & heap_bh6_w13_13_d1 & '0' & '0' & heap_bh6_w10_11_d1 & heap_bh6_w9_11_d1 & heap_bh6_w8_11_d1 & '0' & '0' & heap_bh6_w5_4_d1 & heap_bh6_w4_4_d1 & '0' & heap_bh6_w2_0_d1 & heap_bh6_w1_0_d1;
   finalAdderCin_bh6 <= '0';
   Adder_final6_0: IntAdder_48_f200_uid101  -- pipelineDepth=0 maxInDelay=0
      port map ( clk  => clk,
                 rst  => rst,
                 Cin => finalAdderCin_bh6,
                 R => finalAdderOut_bh6   ,
                 X => finalAdderIn0_bh6,
                 Y => finalAdderIn1_bh6);
   -- concatenate all the compressed chunks
   CompressionResult6 <= finalAdderOut_bh6 & tempR_bh6_0_d1;
   -- End of code generated by BitHeap::generateCompressorVHDL
   R <= CompressionResult6(47 downto 0);
end architecture;

--------------------------------------------------------------------------------
--                          IntAdder_34_f200_uid109
--                    (IntAdderAlternative_34_f200_uid113)
-- This operator is part of the Infinite Virtual Library FloPoCoLib
-- All rights reserved
-- Authors: Bogdan Pasca, Florent de Dinechin (2008-2010)
--------------------------------------------------------------------------------
-- Pipeline depth: 0 cycles

library ieee;
use ieee.std_logic_1164.all;
use ieee.std_logic_arith.all;
use ieee.std_logic_unsigned.all;
library std;
use std.textio.all;
library work;

entity IntAdder_34_f200_uid109 is
   port ( clk, rst : in std_logic;
          X : in  std_logic_vector(33 downto 0);
          Y : in  std_logic_vector(33 downto 0);
          Cin : in  std_logic;
          R : out  std_logic_vector(33 downto 0)   );
end entity;

architecture arch of IntAdder_34_f200_uid109 is
begin
   process(clk)
      begin
         if clk'event and clk = '1' then
         end if;
      end process;
   --Alternative
    R <= X + Y + Cin;
end architecture;

--------------------------------------------------------------------------------
--                                  Mul_Clk
--                        (FPMult_9_23_9_23_9_23_uid2)
-- This operator is part of the Infinite Virtual Library FloPoCoLib
-- All rights reserved
-- Authors: Bogdan Pasca, Florent de Dinechin 2008-2011
--------------------------------------------------------------------------------
-- Pipeline depth: 1 cycles

library ieee;
use ieee.std_logic_1164.all;
use ieee.std_logic_arith.all;
use ieee.std_logic_unsigned.all;
library std;
use std.textio.all;
library work;

entity Mul_Clk is
   port ( clk, rst : in std_logic;
          X : in  std_logic_vector(9+23+2 downto 0);
          Y : in  std_logic_vector(9+23+2 downto 0);
          R : out  std_logic_vector(9+23+2 downto 0);
      round : buffer std_logic;          -- mod by JDH Sept 21, 2015
       sign : buffer std_logic;
    roundit : in std_logic  );
end entity;

architecture arch of Mul_Clk is
   component IntAdder_34_f200_uid109 is
      port ( clk, rst : in std_logic;
             X : in  std_logic_vector(33 downto 0);
             Y : in  std_logic_vector(33 downto 0);
             Cin : in  std_logic;
             R : out  std_logic_vector(33 downto 0)   );
   end component;

   component IntMultiplier_UsingDSP_24_24_48_unsigned_uid4 is
      port ( clk, rst : in std_logic;
             X : in  std_logic_vector(23 downto 0);
             Y : in  std_logic_vector(23 downto 0);
             R : out  std_logic_vector(47 downto 0)   );
   end component;

--signal sign, sign_d1 :  std_logic;            
signal sign_d1 :  std_logic;                 -- mod by JDH Sept 21, 2015
signal expX :  std_logic_vector(8 downto 0);
signal expY :  std_logic_vector(8 downto 0);
signal expSumPreSub :  std_logic_vector(10 downto 0);
signal bias :  std_logic_vector(10 downto 0);
signal expSum, expSum_d1 :  std_logic_vector(10 downto 0);
signal sigX :  std_logic_vector(23 downto 0);
signal sigY :  std_logic_vector(23 downto 0);
signal sigProd :  std_logic_vector(47 downto 0);
signal excSel :  std_logic_vector(3 downto 0);
signal exc, exc_d1 :  std_logic_vector(1 downto 0);
signal norm :  std_logic;
signal expPostNorm :  std_logic_vector(10 downto 0);
signal sigProdExt :  std_logic_vector(47 downto 0);
signal expSig :  std_logic_vector(33 downto 0);
signal sticky :  std_logic;
signal guard :  std_logic;
--signal round :  std_logic;
signal expSigPostRound :  std_logic_vector(33 downto 0);
signal excPostNorm :  std_logic_vector(1 downto 0);
signal finalExc :  std_logic_vector(1 downto 0);
begin
   process(clk)
      begin
         if clk'event and clk = '1' then
            sign_d1 <=  sign;
            expSum_d1 <=  expSum;
            exc_d1 <=  exc;
         end if;
      end process;
   sign <= X(32) xor Y(32);
   expX <= X(31 downto 23);
   expY <= Y(31 downto 23);
   expSumPreSub <= ("00" & expX) + ("00" & expY);
   bias <= CONV_STD_LOGIC_VECTOR(255,11);
   expSum <= expSumPreSub - bias;
   ----------------Synchro barrier, entering cycle 0----------------
   sigX <= "1" & X(22 downto 0);
   sigY <= "1" & Y(22 downto 0);
   SignificandMultiplication: IntMultiplier_UsingDSP_24_24_48_unsigned_uid4  -- pipelineDepth=1 maxInDelay=0
      port map ( clk  => clk,
                 rst  => rst,
                 R => sigProd,
                 X => sigX,
                 Y => sigY);
   ----------------Synchro barrier, entering cycle 1----------------
   ----------------Synchro barrier, entering cycle 0----------------
   excSel <= X(34 downto 33) & Y(34 downto 33);
   with excSel select
   exc <= "00" when  "0000" | "0001" | "0100",
          "01" when "0101",
          "10" when "0110" | "1001" | "1010" ,
          "11" when others;
   ----------------Synchro barrier, entering cycle 1----------------
   norm <= sigProd(47);
   -- exponent update
   expPostNorm <= expSum_d1 + ("0000000000" & norm);
   ----------------Synchro barrier, entering cycle 1----------------
   -- significand normalization shift
   sigProdExt <= sigProd(46 downto 0) & "0" when norm='1' else
                         sigProd(45 downto 0) & "00";
   expSig <= expPostNorm & sigProdExt(47 downto 25);
   sticky <= sigProdExt(24);
   guard <= '0' when sigProdExt(23 downto 0)="000000000000000000000000" else '1';
   round <= sticky and ( (guard and not(sigProdExt(25))) or (sigProdExt(25) ))  ;
   RoundingAdder: IntAdder_34_f200_uid109  -- pipelineDepth=0 maxInDelay=2.82416e-09
      port map ( clk  => clk,
                 rst  => rst,
--                 Cin => round,
                 Cin => roundit,   -- mod by JDH Sept 21, 2015
                 R => expSigPostRound   ,
                 X => expSig,
                 Y => "0000000000000000000000000000000000");
   with expSigPostRound(33 downto 32) select
   excPostNorm <=  "01"  when  "00",
                               "10"             when "01",
                               "00"             when "11"|"10",
                               "11"             when others;
   with exc_d1 select
   finalExc <= exc_d1 when  "11"|"10"|"00",
                       excPostNorm when others;
   R <= finalExc & sign_d1 & expSigPostRound(31 downto 0);
end architecture;
